vgacentrifuge/pcb/centrifuge_combined/centrifuge.kicad_sch

## KiCad design centrifuge_combined/centrifuge.kicad_sch (2022-10-28)

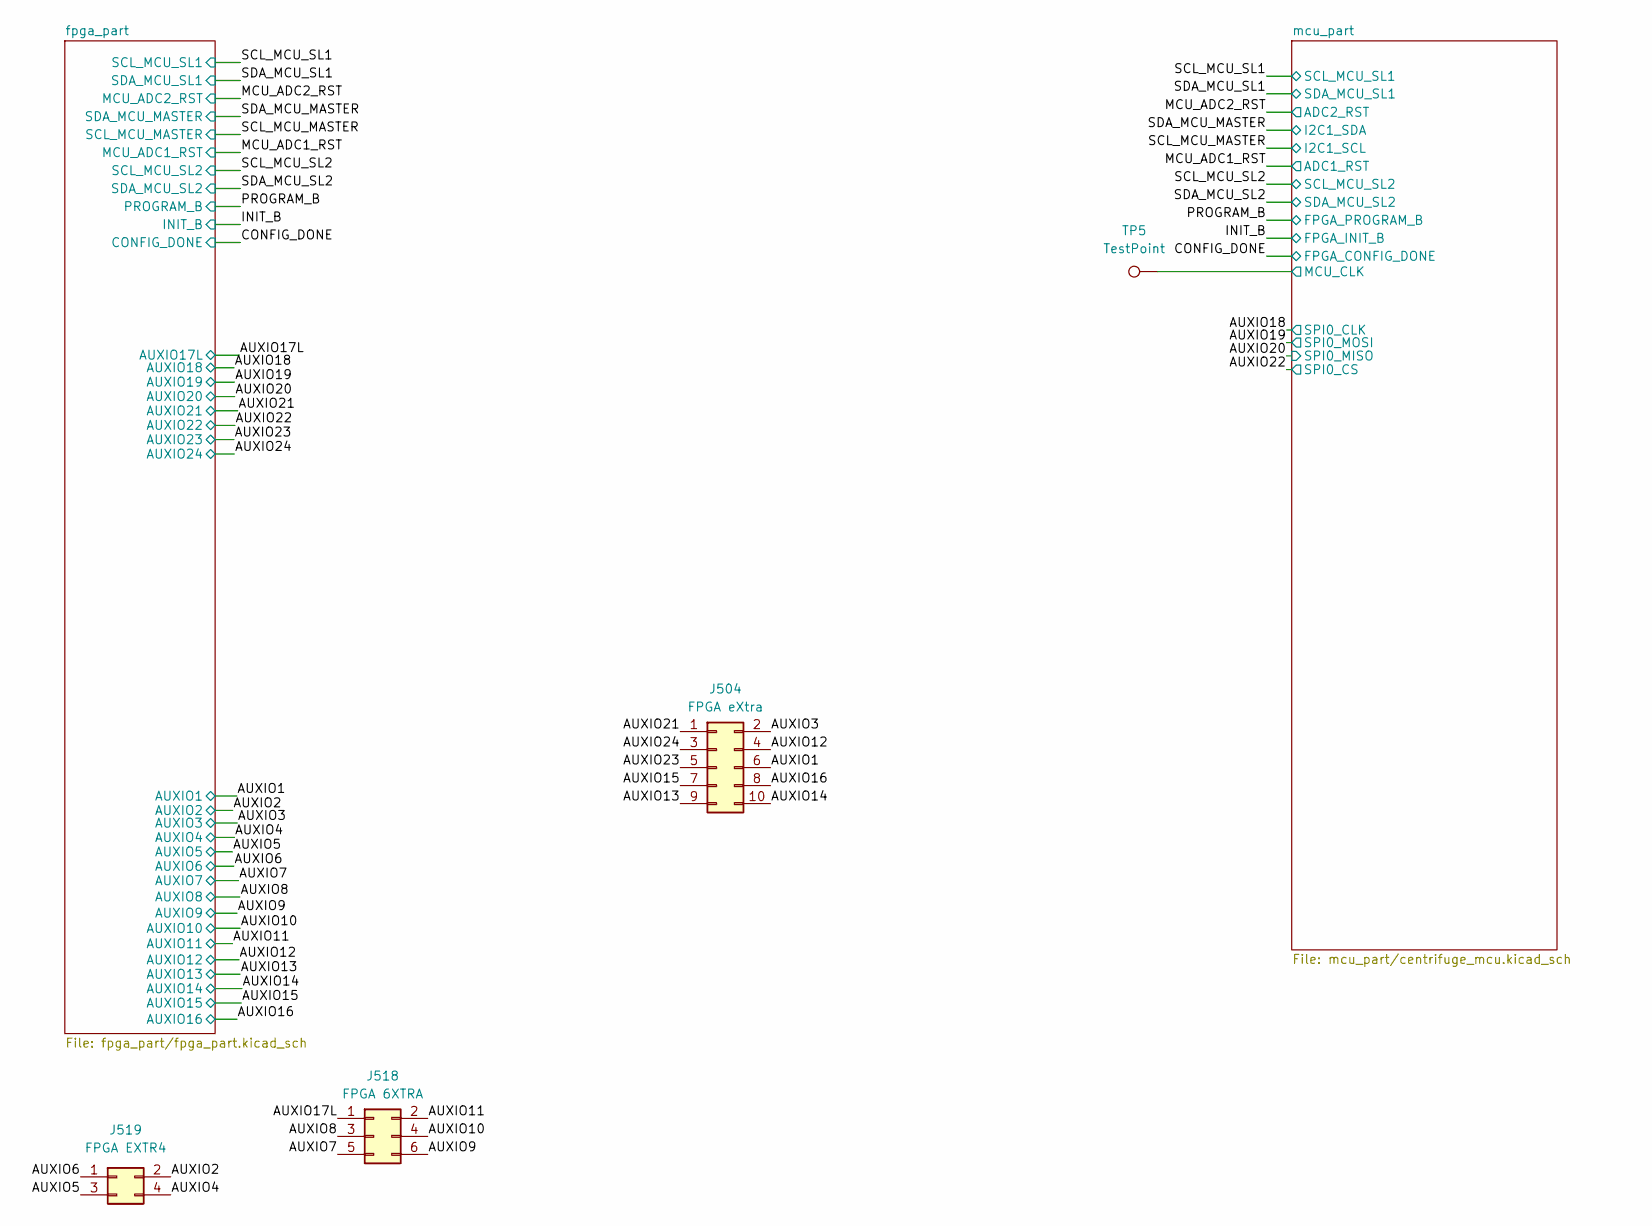
[picture p18: schematic centrifuge.kicad_sch]

Parts:
J504: FPGA eXtra; PinHeader_2x05_P2.54mm_Vertical
J518: FPGA 6XTRA; PinHeader_2x03_P2.54mm_Vertical
J519: FPGA EXTR4; PinHeader_2x02_P2.54mm_Vertical
TP5: TestPoint; TestPoint_Keystone_5015_Micro-Minature

Connections:
AUXIO1: J504.6
AUXIO2: J519.2
AUXIO3: J504.2
AUXIO4: J519.4
AUXIO5: J519.3
AUXIO6: J519.1
AUXIO7: J518.5
AUXIO8: J518.3
AUXIO9: J518.6
AUXIO10: J518.4
AUXIO11: J518.2
AUXIO12: J504.4
AUXIO13: J504.9
AUXIO14: J504.10
AUXIO15: J504.7
AUXIO16: J504.8
AUXIO17L: J518.1
AUXIO21: J504.1
AUXIO23: J504.5
AUXIO24: J504.3
MCU_CLK: TP5.1
