vgacentrifuge/pcb/centrifuge_combined/fpga_part/config_sram.kicad_sch

## KiCad design centrifuge_combined/fpga_part/config_sram.kicad_sch (2022-10-22)

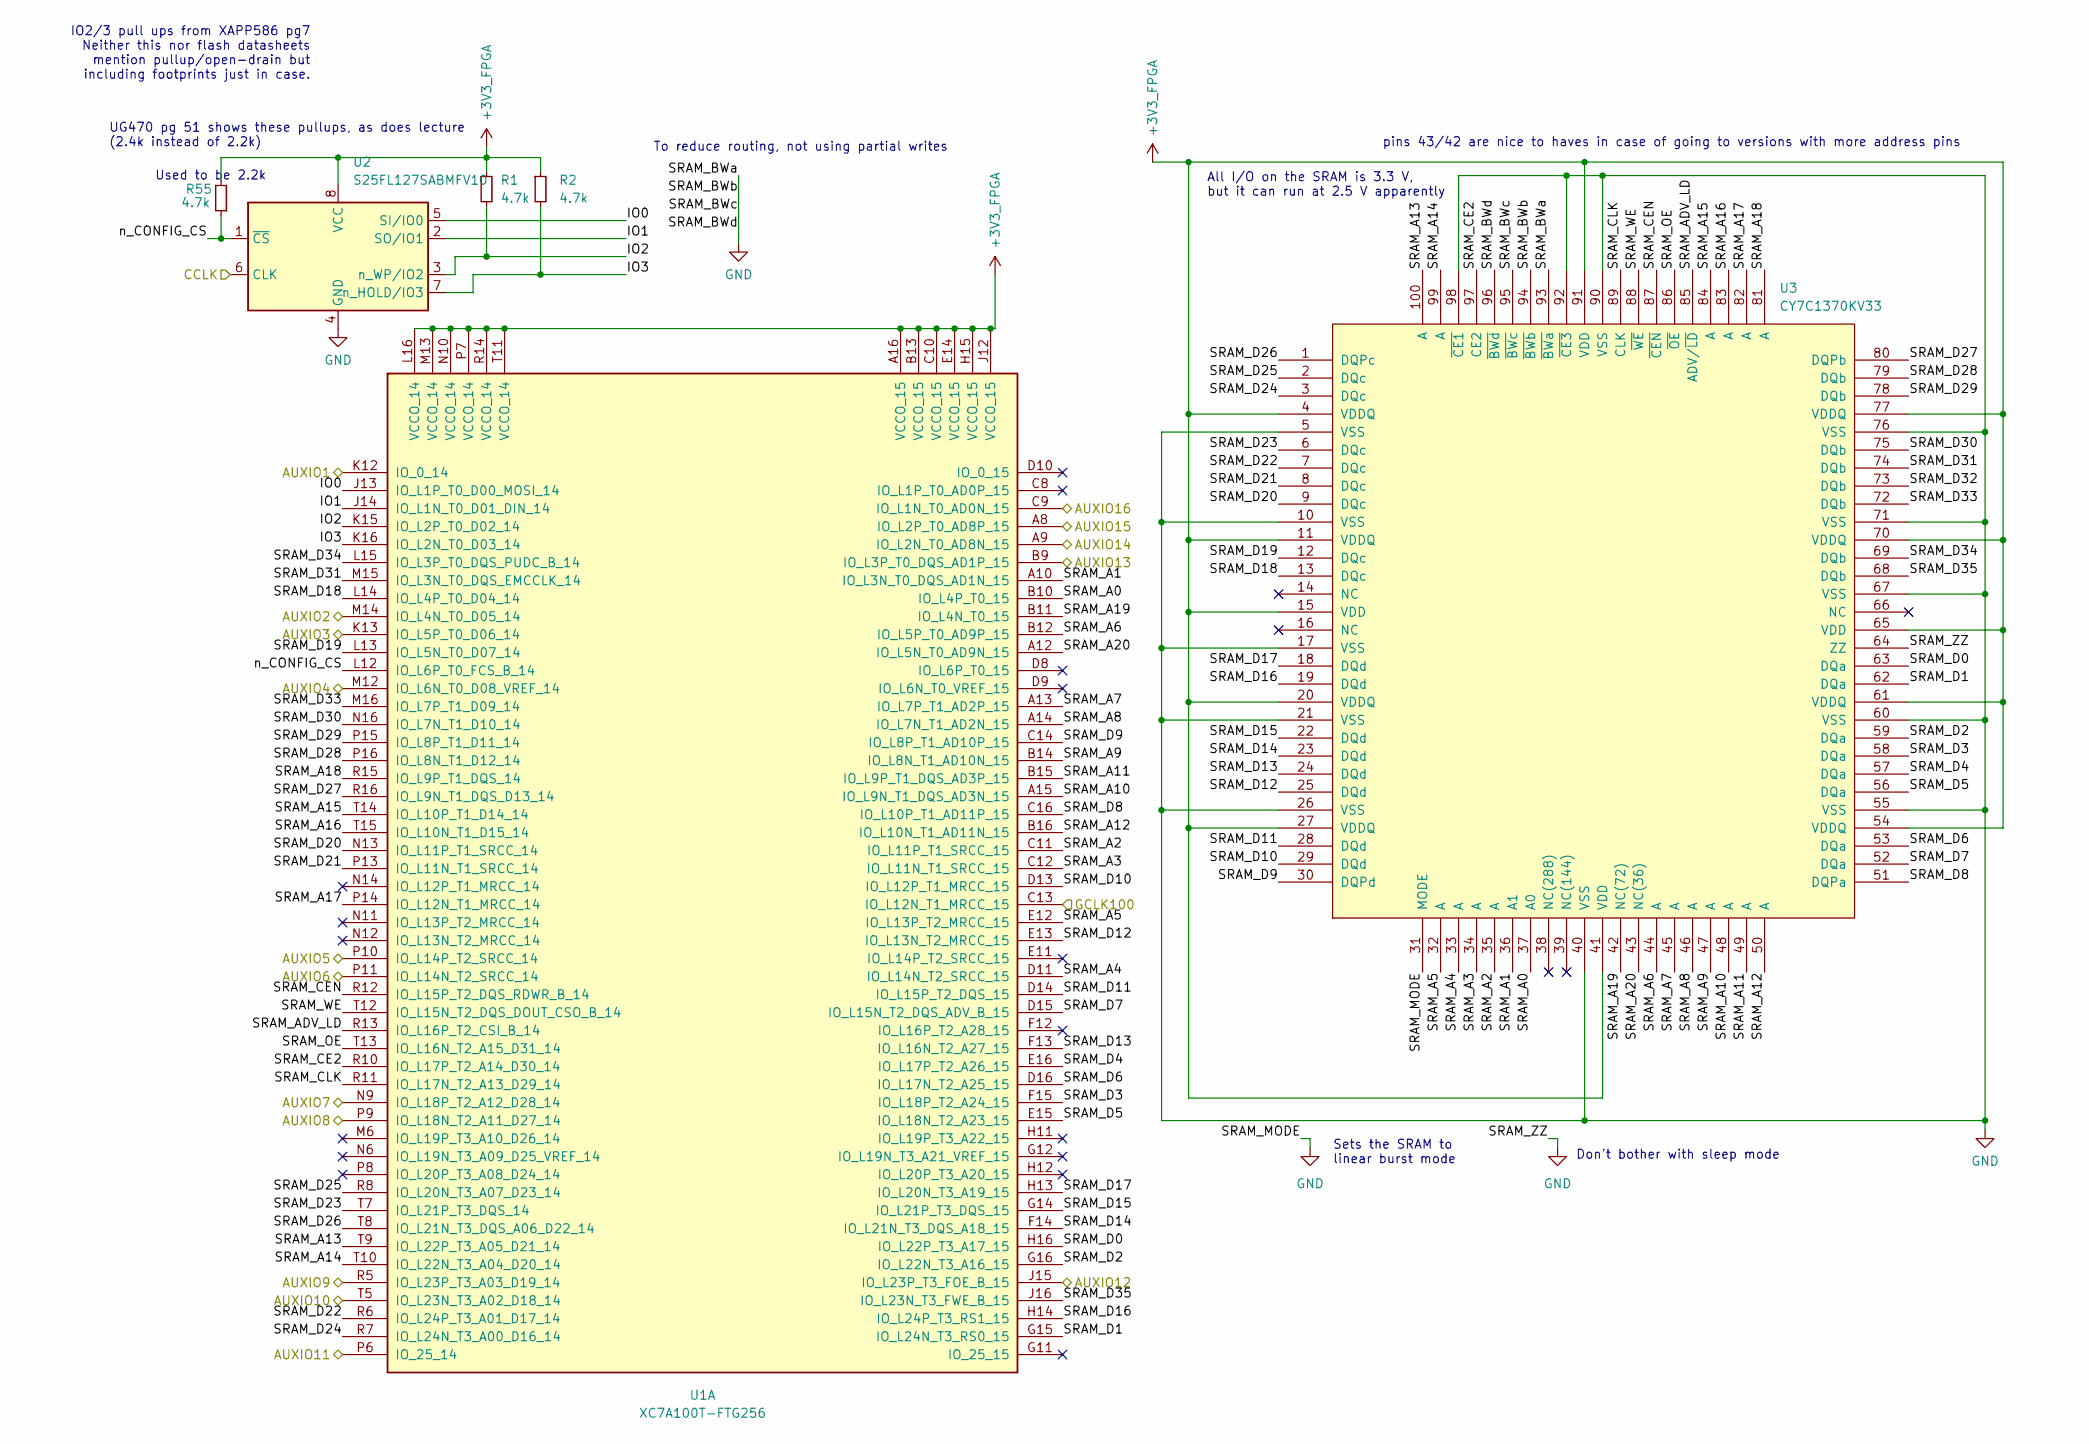
[picture p19: schematic config_sram.kicad_sch]

Parts:
R1, R2, R55: 4.7k; R_0805_2012Metric_Pad1.20x1.40mm_HandSolder
U1: XC7A100T-FTG256; Xilinx_FTG256
U2: S25FL127SABMFV10; SOIC-8_5.23x5.23mm_P1.27mm
U3: CY7C1370KV33; PQFP-100_14x20mm_P0.65mm

Connections:
+3V3_FPGA: R1.1, R2.1, R55.2, U1.A16 (VCCO_15), U1.B13 (VCCO_15), U1.C10 (VCCO_15), U1.E14 (VCCO_15), U1.H15 (VCCO_15), U1.J12 (VCCO_15), U1.L16 (VCCO_14), U1.M13 (VCCO_14), U1.N10 (VCCO_14), U1.P7 (VCCO_14), U1.R14 (VCCO_14), U1.T11 (VCCO_14), U2.8 (VCC), U3.4 (VDDQ), U3.11 (VDDQ), U3.15 (VDD), U3.20 (VDDQ), U3.27 (VDDQ), U3.41 (VDD), U3.54 (VDDQ), U3.61 (VDDQ), U3.65 (VDD), U3.70 (VDDQ), U3.77 (VDDQ), U3.91 (VDD)
AUXIO1: U1.K12 (IO_0_14)
AUXIO2: U1.M14 (IO_L4N_T0_D05_14)
AUXIO3: U1.K13 (IO_L5P_T0_D06_14)
AUXIO4: U1.M12 (IO_L6N_T0_D08_VREF_14)
AUXIO5: U1.P10 (IO_L14P_T2_SRCC_14)
AUXIO6: U1.P11 (IO_L14N_T2_SRCC_14)
AUXIO7: U1.N9 (IO_L18P_T2_A12_D28_14)
AUXIO8: U1.P9 (IO_L18N_T2_A11_D27_14)
AUXIO9: U1.R5 (IO_L23P_T3_A03_D19_14)
AUXIO10: U1.T5 (IO_L23N_T3_A02_D18_14)
AUXIO11: U1.P6 (IO_25_14)
AUXIO12: U1.J15 (IO_L23P_T3_FOE_B_15)
AUXIO13: U1.B9 (IO_L3P_T0_DQS_AD1P_15)
AUXIO14: U1.A9 (IO_L2N_T0_AD8N_15)
AUXIO15: U1.A8 (IO_L2P_T0_AD8P_15)
AUXIO16: U1.C9 (IO_L1N_T0_AD0N_15)
CCLK: U2.6 (CLK)
GCLK100: U1.C13 (IO_L12N_T1_MRCC_15)
GND: U2.4 (GND), U3.5 (VSS), U3.10 (VSS), U3.17 (VSS), U3.21 (VSS), U3.26 (VSS), U3.31 (MODE), U3.40 (VSS), U3.55 (VSS), U3.60 (VSS), U3.64 (ZZ), U3.67 (VSS), U3.71 (VSS), U3.76 (VSS), U3.90 (VSS), U3.92 (~CE3), U3.93 (~BWa), U3.94 (~BWb), U3.95 (~BWc), U3.96 (~BWd), U3.98 (~CE1)
IO0: U1.J13 (IO_L1P_T0_D00_MOSI_14), U2.5 (SI/IO0)
IO1: U1.J14 (IO_L1N_T0_D01_DIN_14), U2.2 (SO/IO1)
IO2: R1.2, U1.K15 (IO_L2P_T0_D02_14), U2.3 (n_WP/IO2)
IO3: R2.2, U1.K16 (IO_L2N_T0_D03_14), U2.7 (n_HOLD/IO3)
SRAM_A0: U1.B10 (IO_L4P_T0_15), U3.37 (A0)
SRAM_A1: U1.A10 (IO_L3N_T0_DQS_AD1N_15), U3.36 (A1)
SRAM_A2: U1.C11 (IO_L11P_T1_SRCC_15), U3.35 (A)
SRAM_A3: U1.C12 (IO_L11N_T1_SRCC_15), U3.34 (A)
SRAM_A4: U1.D11 (IO_L14N_T2_SRCC_15), U3.33 (A)
SRAM_A5: U1.E12 (IO_L13P_T2_MRCC_15), U3.32 (A)
SRAM_A6: U1.B12 (IO_L5P_T0_AD9P_15), U3.44 (A)
SRAM_A7: U1.A13 (IO_L7P_T1_AD2P_15), U3.45 (A)
SRAM_A8: U1.A14 (IO_L7N_T1_AD2N_15), U3.46 (A)
SRAM_A9: U1.B14 (IO_L8N_T1_AD10N_15), U3.47 (A)
SRAM_A10: U1.A15 (IO_L9N_T1_DQS_AD3N_15), U3.48 (A)
SRAM_A11: U1.B15 (IO_L9P_T1_DQS_AD3P_15), U3.49 (A)
SRAM_A12: U1.B16 (IO_L10N_T1_AD11N_15), U3.50 (A)
SRAM_A13: U1.T9 (IO_L22P_T3_A05_D21_14), U3.100 (A)
SRAM_A14: U1.T10 (IO_L22N_T3_A04_D20_14), U3.99 (A)
SRAM_A15: U1.T14 (IO_L10P_T1_D14_14), U3.84 (A)
SRAM_A16: U1.T15 (IO_L10N_T1_D15_14), U3.83 (A)
SRAM_A17: U1.P14 (IO_L12N_T1_MRCC_14), U3.82 (A)
SRAM_A18: U1.R15 (IO_L9P_T1_DQS_14), U3.81 (A)
SRAM_A19: U1.B11 (IO_L4N_T0_15), U3.42 (NC(72))
SRAM_A20: U1.A12 (IO_L5N_T0_AD9N_15), U3.43 (NC(36))
SRAM_ADV_LD: U1.R13 (IO_L16P_T2_CSI_B_14), U3.85 (ADV/~LD)
SRAM_CE2: U1.R10 (IO_L17P_T2_A14_D30_14), U3.97 (CE2)
SRAM_CEN: U1.R12 (IO_L15P_T2_DQS_RDWR_B_14), U3.87 (~CEN)
SRAM_CLK: U1.R11 (IO_L17N_T2_A13_D29_14), U3.89 (CLK)
SRAM_D0: U1.H16 (IO_L22P_T3_A17_15), U3.63 (DQa)
SRAM_D1: U1.G15 (IO_L24N_T3_RS0_15), U3.62 (DQa)
SRAM_D2: U1.G16 (IO_L22N_T3_A16_15), U3.59 (DQa)
SRAM_D3: U1.F15 (IO_L18P_T2_A24_15), U3.58 (DQa)
SRAM_D4: U1.E16 (IO_L17P_T2_A26_15), U3.57 (DQa)
SRAM_D5: U1.E15 (IO_L18N_T2_A23_15), U3.56 (DQa)
SRAM_D6: U1.D16 (IO_L17N_T2_A25_15), U3.53 (DQa)
SRAM_D7: U1.D15 (IO_L15N_T2_DQS_ADV_B_15), U3.52 (DQa)
SRAM_D8: U1.C16 (IO_L10P_T1_AD11P_15), U3.51 (DQPa)
SRAM_D9: U1.C14 (IO_L8P_T1_AD10P_15), U3.30 (DQPd)
SRAM_D10: U1.D13 (IO_L12P_T1_MRCC_15), U3.29 (DQd)
SRAM_D11: U1.D14 (IO_L15P_T2_DQS_15), U3.28 (DQd)
SRAM_D12: U1.E13 (IO_L13N_T2_MRCC_15), U3.25 (DQd)
SRAM_D13: U1.F13 (IO_L16N_T2_A27_15), U3.24 (DQd)
SRAM_D14: U1.F14 (IO_L21N_T3_DQS_A18_15), U3.23 (DQd)
SRAM_D15: U1.G14 (IO_L21P_T3_DQS_15), U3.22 (DQd)
SRAM_D16: U1.H14 (IO_L24P_T3_RS1_15), U3.19 (DQd)
SRAM_D17: U1.H13 (IO_L20N_T3_A19_15), U3.18 (DQd)
SRAM_D18: U1.L14 (IO_L4P_T0_D04_14), U3.13 (DQc)
SRAM_D19: U1.L13 (IO_L5N_T0_D07_14), U3.12 (DQc)
SRAM_D20: U1.N13 (IO_L11P_T1_SRCC_14), U3.9 (DQc)
SRAM_D21: U1.P13 (IO_L11N_T1_SRCC_14), U3.8 (DQc)
SRAM_D22: U1.R6 (IO_L24P_T3_A01_D17_14), U3.7 (DQc)
SRAM_D23: U1.T7 (IO_L21P_T3_DQS_14), U3.6 (DQc)
SRAM_D24: U1.R7 (IO_L24N_T3_A00_D16_14), U3.3 (DQc)
SRAM_D25: U1.R8 (IO_L20N_T3_A07_D23_14), U3.2 (DQc)
SRAM_D26: U1.T8 (IO_L21N_T3_DQS_A06_D22_14), U3.1 (DQPc)
SRAM_D27: U1.R16 (IO_L9N_T1_DQS_D13_14), U3.80 (DQPb)
SRAM_D28: U1.P16 (IO_L8N_T1_D12_14), U3.79 (DQb)
SRAM_D29: U1.P15 (IO_L8P_T1_D11_14), U3.78 (DQb)
SRAM_D30: U1.N16 (IO_L7N_T1_D10_14), U3.75 (DQb)
SRAM_D31: U1.M15 (IO_L3N_T0_DQS_EMCCLK_14), U3.74 (DQb)
SRAM_D32: U3.73 (DQb)
SRAM_D33: U1.M16 (IO_L7P_T1_D09_14), U3.72 (DQb)
SRAM_D34: U1.L15 (IO_L3P_T0_DQS_PUDC_B_14), U3.69 (DQb)
SRAM_D35: U1.J16 (IO_L23N_T3_FWE_B_15), U3.68 (DQb)
SRAM_OE: U1.T13 (IO_L16N_T2_A15_D31_14), U3.86 (~OE)
SRAM_WE: U1.T12 (IO_L15N_T2_DQS_DOUT_CSO_B_14), U3.88 (~WE)
n_CONFIG_CS: R55.1, U1.L12 (IO_L6P_T0_FCS_B_14), U2.1 (~CS)

Notes on the sheet:
Don't bother with sleep mode
Sets the SRAM to linear burst mode
Used to be 2.2k
IO2/3 pull ups from XAPP586 pg7 Neither this nor flash datasheets mention pullup/open-drain but including footprints just in case.
UG470 pg 51 shows these pullups, as does lecture (2.4k instead of 2.2k)
All I/O on the SRAM is 3.3 V, but it can run at 2.5 V apparently
To reduce routing, not using partial writes
pins 43/42 are nice to haves in case of going to versions with more address pins
