vgacentrifuge/pcb/centrifuge_combined/fpga_part/ddc_eeprom.kicad_sch

## KiCad design centrifuge_combined/fpga_part/ddc_eeprom.kicad_sch (2022-11-09)

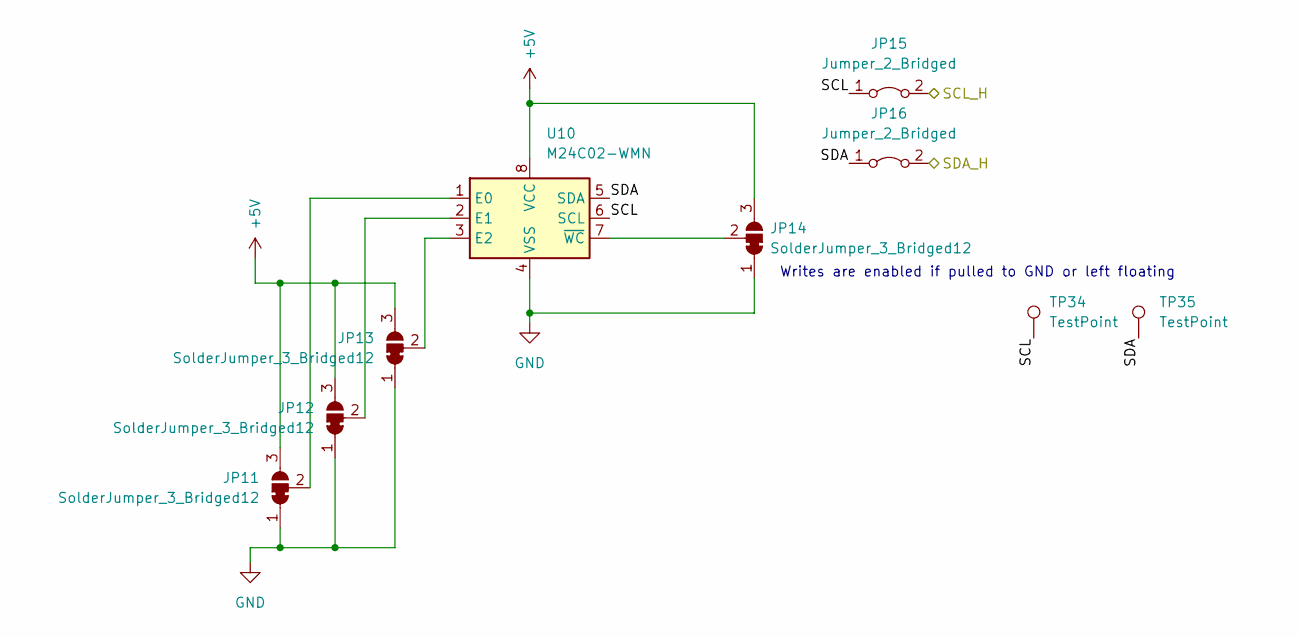
[picture p20: schematic ddc_eeprom.kicad_sch]

Parts:
JP11, JP12, JP13, JP14: SolderJumper_3_Bridged12; SolderJumper-3_P1.3mm_Open_Pad1.0x1.5mm_NumberLabels
JP15, JP16: Jumper_2_Bridged; SolderJumper-2_P1.3mm_Bridged_Pad1.0x1.5mm
TP34, TP35: TestPoint; TestPoint_Keystone_5015_Micro-Minature
U10: M24C02-WMN; SOIC-8_3.9x4.9mm_P1.27mm

Connections:
+5V: JP11.3 (B), JP12.3 (B), JP13.3 (B), JP14.3 (B), U10.8 (VCC)
GND: JP11.1 (A), JP12.1 (A), JP13.1 (A), JP14.1 (A), U10.4 (VSS)
unnamed: JP11.2 (C), U10.1 (E0)
unnamed: JP12.2 (C), U10.2 (E1)
unnamed: JP13.2 (C), U10.3 (E2)
unnamed: JP14.2 (C), U10.7 (~WC)
SCL: JP15.1 (A), TP34.1, U10.6 (SCL)
SCL_H: JP15.2 (B)
SDA: JP16.1 (A), TP35.1, U10.5 (SDA)
SDA_H: JP16.2 (B)

Notes on the sheet:
Writes are enabled if pulled to GND or left floating
