vgacentrifuge/pcb/centrifuge_combined/fpga_part/fpga_core.kicad_sch

## KiCad design centrifuge_combined/fpga_part/fpga_core.kicad_sch (2022-11-09)

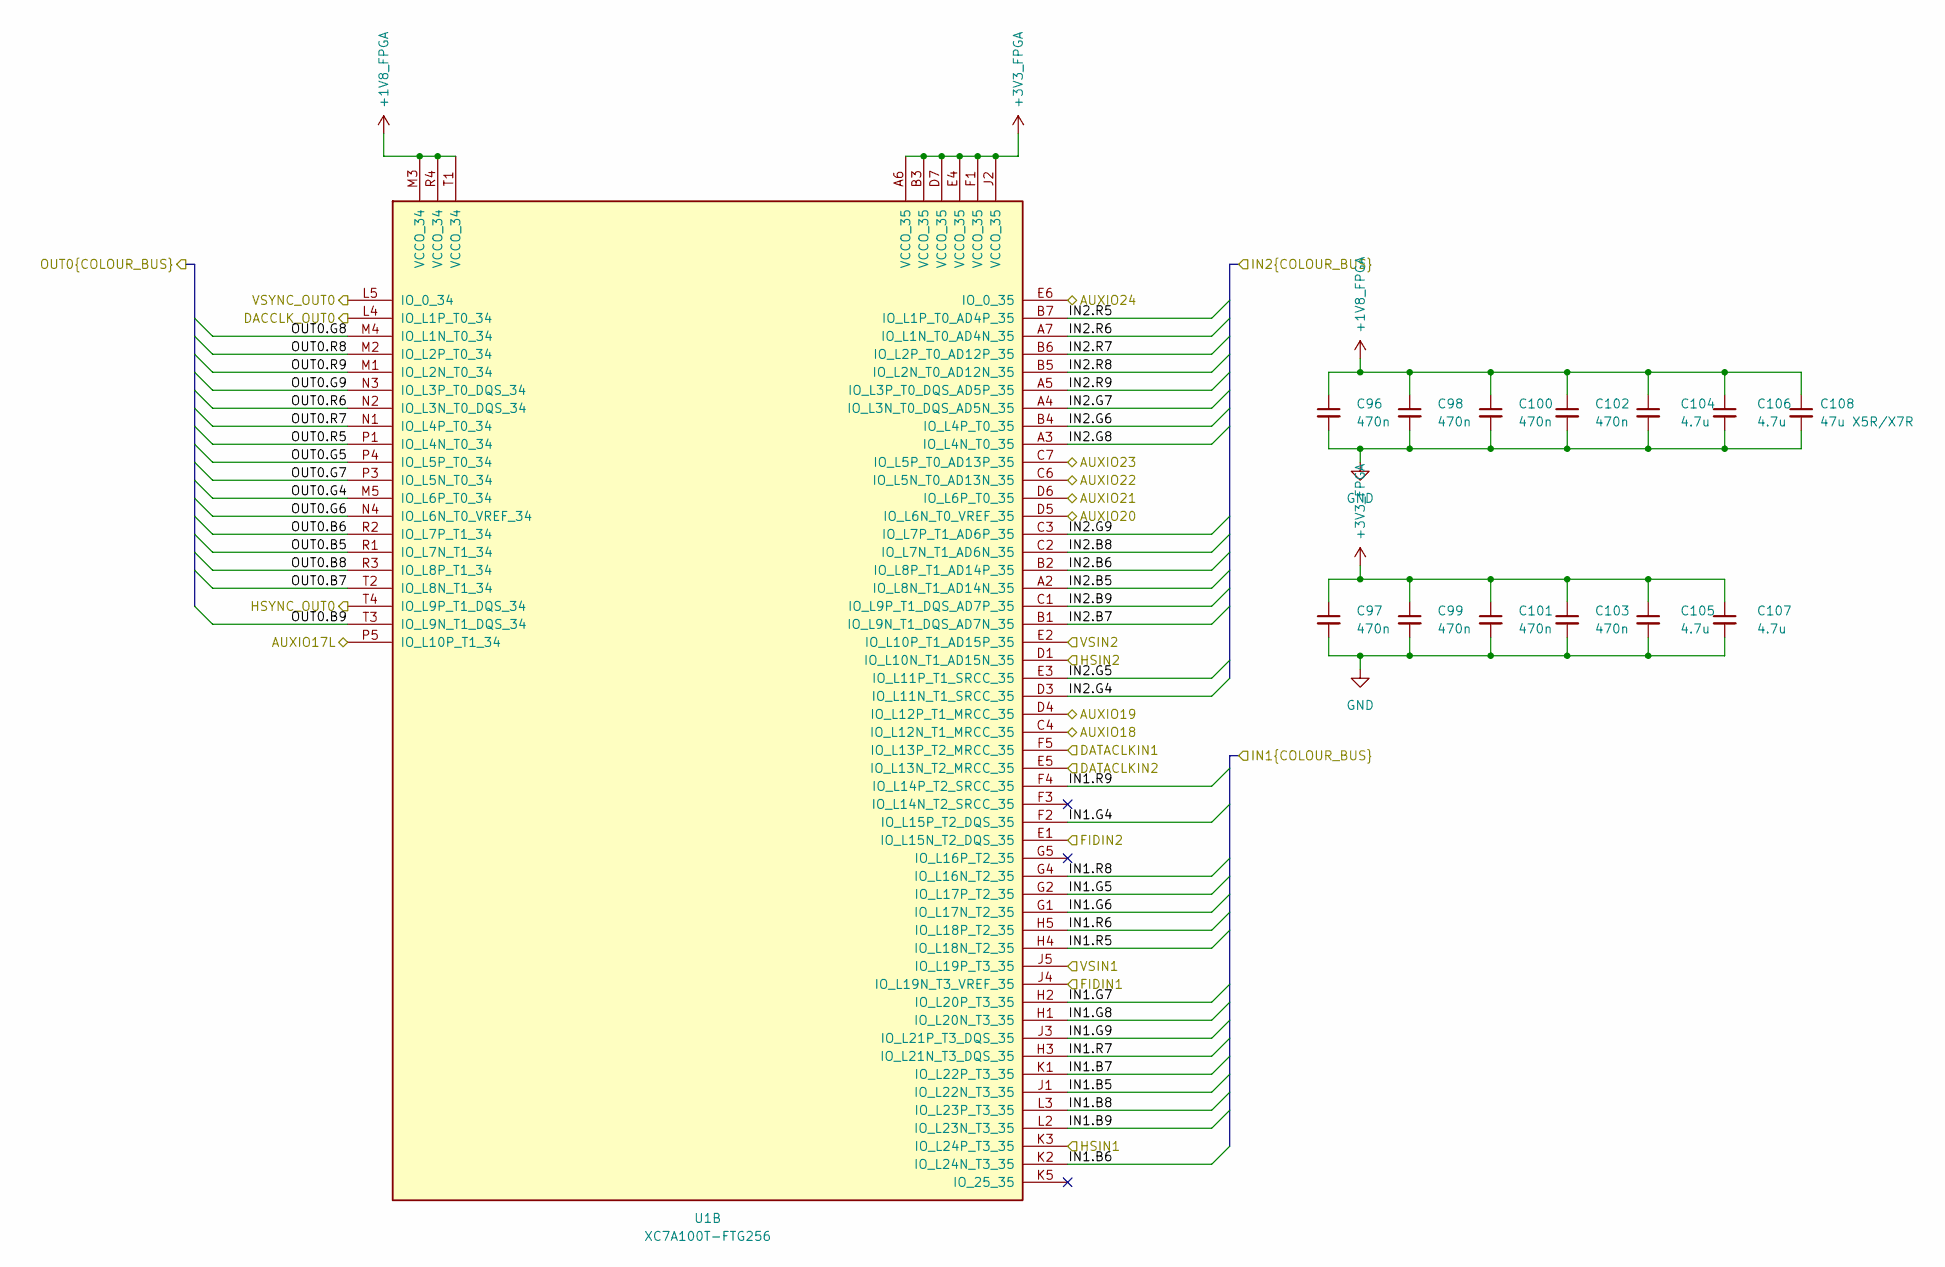
[picture p21: schematic fpga_core.kicad_sch]

Parts:
C96, C97, C98, C99, C100, C101, C102, C103: 470n; C_0603_1608Metric_Pad1.08x0.95mm_HandSolder
C104, C105, C106, C107: 4.7u; C_0805_2012Metric_Pad1.18x1.45mm_HandSolder
C108: 47u X5R/X7R; C_1210_3225Metric_Pad1.33x2.70mm_HandSolder
U1: XC7A100T-FTG256; Xilinx_FTG256

Connections:
+1V8_FPGA: C96.1, C98.1, C100.1, C102.1, C104.1, C106.1, C108.1, U1.M3 (VCCO_34), U1.R4 (VCCO_34), U1.T1 (VCCO_34)
+3V3_FPGA: C97.1, C99.1, C101.1, C103.1, C105.1, C107.1, U1.A6 (VCCO_35), U1.B3 (VCCO_35), U1.D7 (VCCO_35), U1.E4 (VCCO_35), U1.F1 (VCCO_35), U1.J2 (VCCO_35)
AUXIO17L: U1.P5 (IO_L10P_T1_34)
AUXIO18: U1.C4 (IO_L12N_T1_MRCC_35)
AUXIO19: U1.D4 (IO_L12P_T1_MRCC_35)
AUXIO20: U1.D5 (IO_L6N_T0_VREF_35)
AUXIO21: U1.D6 (IO_L6P_T0_35)
AUXIO22: U1.C6 (IO_L5N_T0_AD13N_35)
AUXIO23: U1.C7 (IO_L5P_T0_AD13P_35)
AUXIO24: U1.E6 (IO_0_35)
DACCLK_OUT0: U1.L4 (IO_L1P_T0_34)
DATACLKIN1: U1.F5 (IO_L13P_T2_MRCC_35)
DATACLKIN2: U1.E5 (IO_L13N_T2_MRCC_35)
FIDIN1: U1.J4 (IO_L19N_T3_VREF_35)
FIDIN2: U1.E1 (IO_L15N_T2_DQS_35)
GND: C96.2, C97.2, C98.2, C99.2, C100.2, C101.2, C102.2, C103.2, C104.2, C105.2, C106.2, C107.2, C108.2
HSIN1: U1.K3 (IO_L24P_T3_35)
HSIN2: U1.D1 (IO_L10N_T1_AD15N_35)
HSYNC_OUT0: U1.T4 (IO_L9P_T1_DQS_34)
IN1.B5: U1.J1 (IO_L22N_T3_35)
IN1.B6: U1.K2 (IO_L24N_T3_35)
IN1.B7: U1.K1 (IO_L22P_T3_35)
IN1.B8: U1.L3 (IO_L23P_T3_35)
IN1.B9: U1.L2 (IO_L23N_T3_35)
IN1.G4: U1.F2 (IO_L15P_T2_DQS_35)
IN1.G5: U1.G2 (IO_L17P_T2_35)
IN1.G6: U1.G1 (IO_L17N_T2_35)
IN1.G7: U1.H2 (IO_L20P_T3_35)
IN1.G8: U1.H1 (IO_L20N_T3_35)
IN1.G9: U1.J3 (IO_L21P_T3_DQS_35)
IN1.R5: U1.H4 (IO_L18N_T2_35)
IN1.R6: U1.H5 (IO_L18P_T2_35)
IN1.R7: U1.H3 (IO_L21N_T3_DQS_35)
IN1.R8: U1.G4 (IO_L16N_T2_35)
IN1.R9: U1.F4 (IO_L14P_T2_SRCC_35)
IN2.B5: U1.A2 (IO_L8N_T1_AD14N_35)
IN2.B6: U1.B2 (IO_L8P_T1_AD14P_35)
IN2.B7: U1.B1 (IO_L9N_T1_DQS_AD7N_35)
IN2.B8: U1.C2 (IO_L7N_T1_AD6N_35)
IN2.B9: U1.C1 (IO_L9P_T1_DQS_AD7P_35)
IN2.G4: U1.D3 (IO_L11N_T1_SRCC_35)
IN2.G5: U1.E3 (IO_L11P_T1_SRCC_35)
IN2.G6: U1.B4 (IO_L4P_T0_35)
IN2.G7: U1.A4 (IO_L3N_T0_DQS_AD5N_35)
IN2.G8: U1.A3 (IO_L4N_T0_35)
IN2.G9: U1.C3 (IO_L7P_T1_AD6P_35)
IN2.R5: U1.B7 (IO_L1P_T0_AD4P_35)
IN2.R6: U1.A7 (IO_L1N_T0_AD4N_35)
IN2.R7: U1.B6 (IO_L2P_T0_AD12P_35)
IN2.R8: U1.B5 (IO_L2N_T0_AD12N_35)
IN2.R9: U1.A5 (IO_L3P_T0_DQS_AD5P_35)
OUT0.B5: U1.R1 (IO_L7N_T1_34)
OUT0.B6: U1.R2 (IO_L7P_T1_34)
OUT0.B7: U1.T2 (IO_L8N_T1_34)
OUT0.B8: U1.R3 (IO_L8P_T1_34)
OUT0.B9: U1.T3 (IO_L9N_T1_DQS_34)
OUT0.G4: U1.M5 (IO_L6P_T0_34)
OUT0.G5: U1.P4 (IO_L5P_T0_34)
OUT0.G6: U1.N4 (IO_L6N_T0_VREF_34)
OUT0.G7: U1.P3 (IO_L5N_T0_34)
OUT0.G8: U1.M4 (IO_L1N_T0_34)
OUT0.G9: U1.N3 (IO_L3P_T0_DQS_34)
OUT0.R5: U1.P1 (IO_L4N_T0_34)
OUT0.R6: U1.N2 (IO_L3N_T0_DQS_34)
OUT0.R7: U1.N1 (IO_L4P_T0_34)
OUT0.R8: U1.M2 (IO_L2P_T0_34)
OUT0.R9: U1.M1 (IO_L2N_T0_34)
VSIN1: U1.J5 (IO_L19P_T3_35)
VSIN2: U1.E2 (IO_L10P_T1_AD15P_35)
VSYNC_OUT0: U1.L5 (IO_0_34)
