vgacentrifuge/pcb/centrifuge_combined/fpga_part/fpga_part.kicad_sch

## KiCad design centrifuge_combined/fpga_part/fpga_part.kicad_sch (2022-11-09)

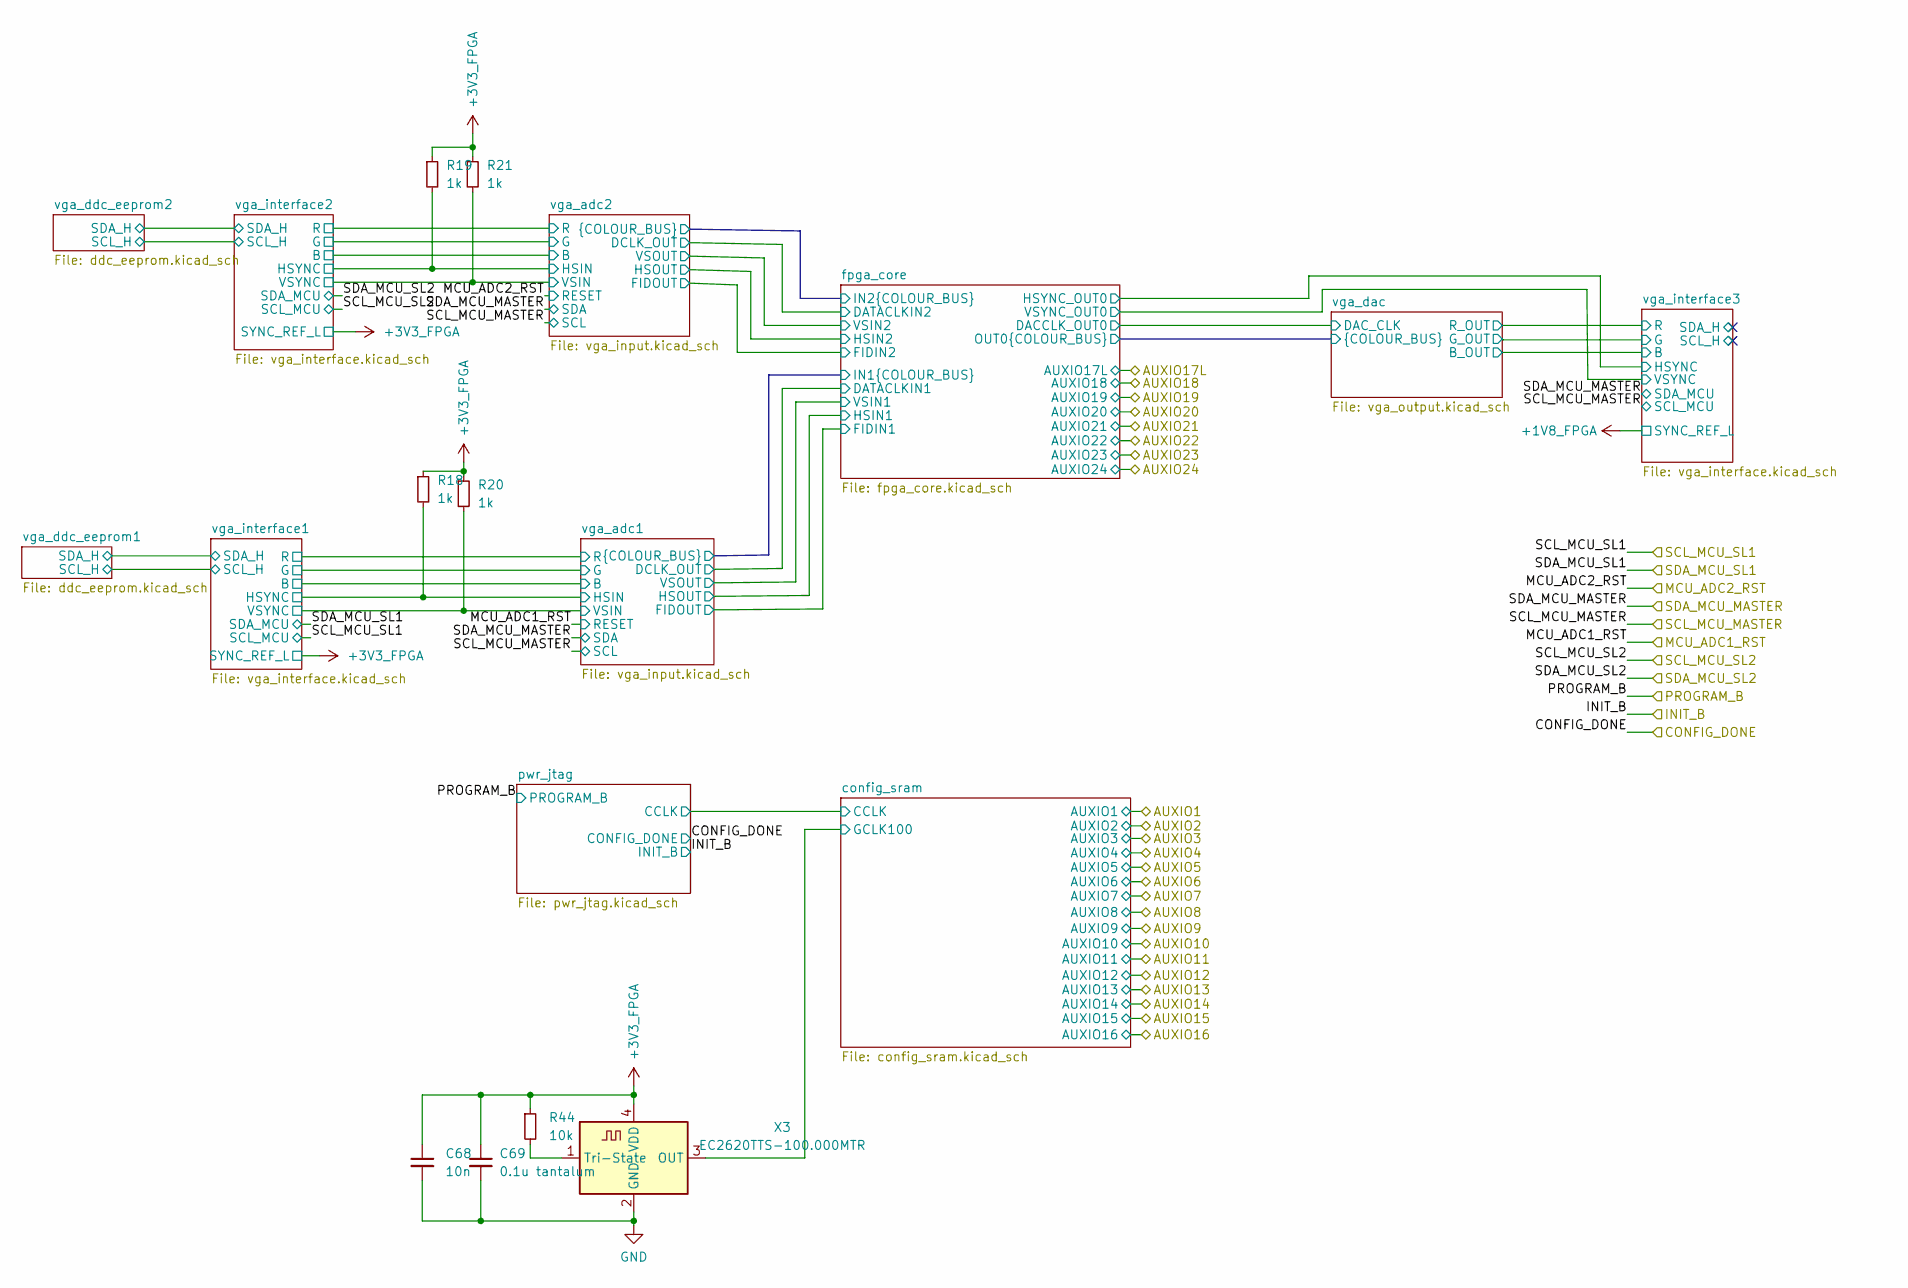
[picture p22: schematic fpga_part.kicad_sch]

Parts:
C68: 10n; C_0805_2012Metric_Pad1.18x1.45mm_HandSolder
C69: 0.1u tantalum; C_0805_2012Metric_Pad1.18x1.45mm_HandSolder
R18, R19, R20, R21: 1k; R_0805_2012Metric_Pad1.20x1.40mm_HandSolder
R44: 10k; R_0805_2012Metric_Pad1.20x1.40mm_HandSolder
X3: EC2620TTS-100.000MTR; Oscillator_SMD_EuroQuartz_XO91-4Pin_7.0x5.0mm_HandSoldering

Connections:
+3V3_FPGA: C68.1, C69.1, R18.1, R19.1, R20.1, R21.1, R44.1, X3.4 (VDD)
GCLK100: X3.3 (OUT)
GND: C68.2, C69.2, X3.2 (GND)
HSYNC: R18.2, R19.2
unnamed: R44.2, X3.1 (Tri-State)
VSYNC: R20.2, R21.2
