vgacentrifuge/pcb/centrifuge_combined/fpga_part/pwr_jtag.kicad_sch

## KiCad design centrifuge_combined/fpga_part/pwr_jtag.kicad_sch (2022-10-13)

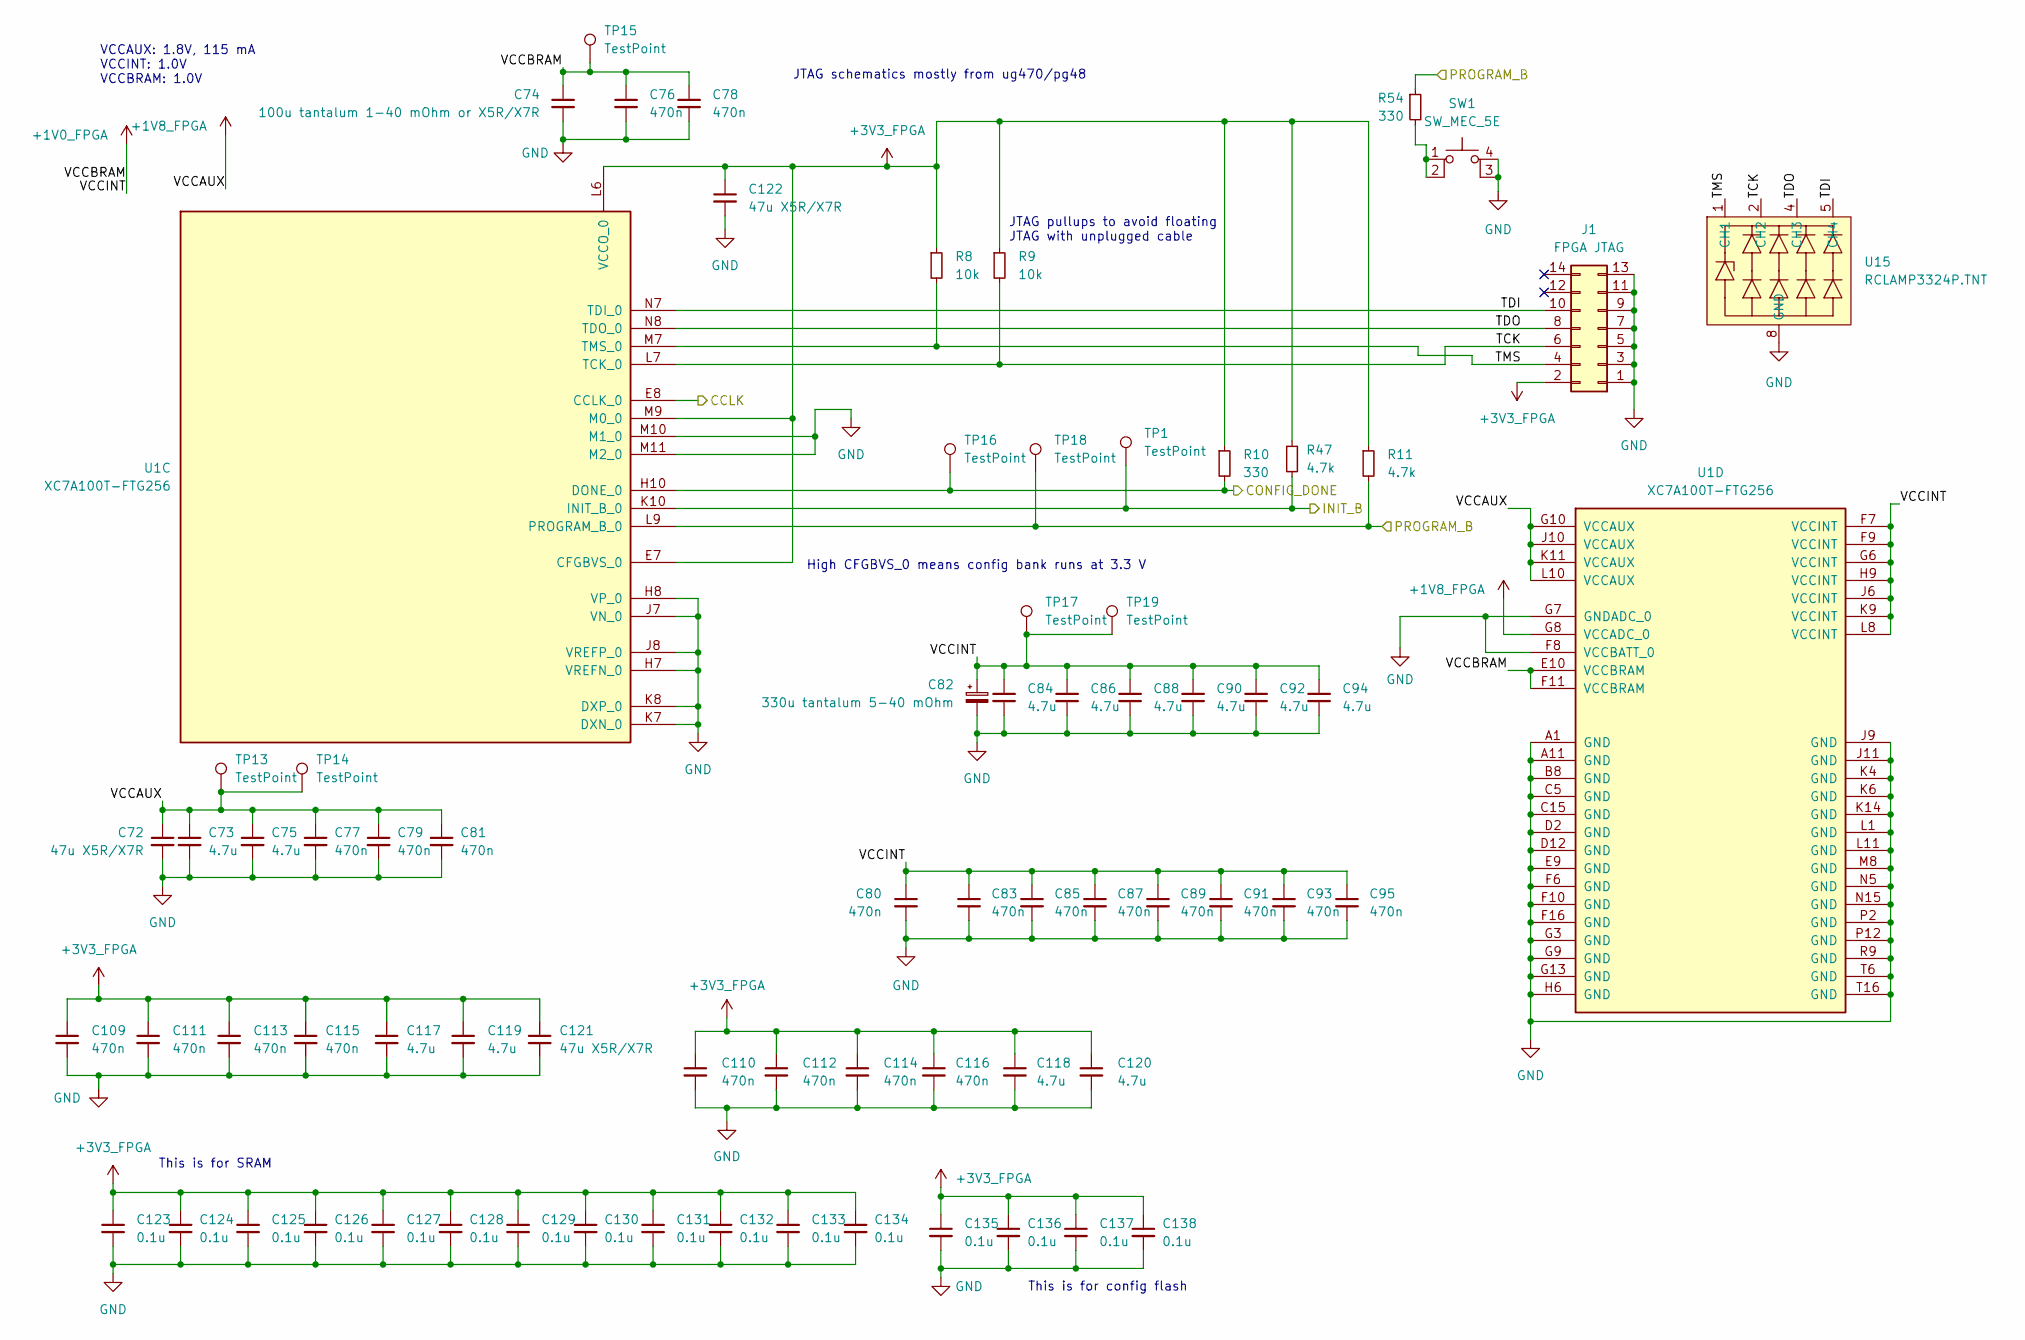
[picture p23: schematic pwr_jtag.kicad_sch]

Parts:
C72, C121, C122: 47u X5R/X7R; C_1210_3225Metric_Pad1.33x2.70mm_HandSolder
C73, C75, C84, C86, C88, C90, C92, C94, C117, C118, C119, C120: 4.7u; C_0805_2012Metric_Pad1.18x1.45mm_HandSolder
C74: 100u tantalum 1-40 mOhm or X5R/X7R; C_1210_3225Metric_Pad1.33x2.70mm_HandSolder
C76, C77, C78, C79, C80, C81, C83, C85, C87, C89, C91, C93, C95, C109, C110, C111, C112, C113, C114, C115, C116: 470n; C_0603_1608Metric_Pad1.08x0.95mm_HandSolder
C82: 330u tantalum 5-40 mOhm; CP_EIA-7343-31_Kemet-D_Pad2.25x2.55mm_HandSolder
C123, C124, C125, C126, C127, C128, C129, C130, C131, C132, C133, C134, C135, C136, C137, C138: 0.1u; C_0805_2012Metric_Pad1.18x1.45mm_HandSolder
J1: FPGA JTAG; 878311411
R8, R9: 10k; R_0805_2012Metric_Pad1.20x1.40mm_HandSolder
R10, R54: 330; R_0805_2012Metric_Pad1.20x1.40mm_HandSolder
R11, R47: 4.7k; R_0805_2012Metric_Pad1.20x1.40mm_HandSolder
SW1: SW_MEC_5E; SW_Push_1P1T_NO_6x6mm_H9.5mm_modified
TP1, TP13, TP14, TP15, TP16, TP17, TP18, TP19: TestPoint; TestPoint_Keystone_5015_Micro-Minature
U1: XC7A100T-FTG256; Xilinx_FTG256
U15: RCLAMP3324P.TNT; Diodes_UDFN-10_1.0x2.5mm_P0.5mm

Connections:
+1V0_FPGA: C74.1, C76.1, C78.1, C80.1, C82.1, C83.1, C84.1, C85.1, C86.1, C87.1, C88.1, C89.1, C90.1, C91.1, C92.1, C93.1, C94.1, C95.1, TP15.1, TP17.1, TP19.1, U1.E10 (VCCBRAM), U1.F7 (VCCINT), U1.F9 (VCCINT), U1.F11 (VCCBRAM), U1.G6 (VCCINT), U1.H9 (VCCINT), U1.J6 (VCCINT), U1.K9 (VCCINT), U1.L8 (VCCINT)
+1V8_FPGA: C72.1, C73.1, C75.1, C77.1, C79.1, C81.1, TP13.1, TP14.1, U1.G8 (VCCADC_0), U1.G10 (VCCAUX), U1.J10 (VCCAUX), U1.K11 (VCCAUX), U1.L10 (VCCAUX)
+3V3_FPGA: C109.1, C110.1, C111.1, C112.1, C113.1, C114.1, C115.1, C116.1, C117.1, C118.1, C119.1, C120.1, C121.1, C122.1, C123.1, C124.1, C125.1, C126.1, C127.1, C128.1, C129.1, C130.1, C131.1, C132.1, C133.1, C134.1, C135.1, C136.1, C137.1, C138.1, J1.2, R8.1, R9.1, R10.1, R11.1, R47.1, U1.E7 (CFGBVS_0), U1.L6 (VCCO_0), U1.M9 (M0_0)
CCLK: U1.E8 (CCLK_0)
CONFIG_DONE: R10.2, TP16.1, U1.H10 (DONE_0)
GND: C72.2, C73.2, C74.2, C75.2, C76.2, C77.2, C78.2, C79.2, C80.2, C81.2, C82.2, C83.2, C84.2, C85.2, C86.2, C87.2, C88.2, C89.2, C90.2, C91.2, C92.2, C93.2, C94.2, C95.2, C109.2, C110.2, C111.2, C112.2, C113.2, C114.2, C115.2, C116.2, C117.2, C118.2, C119.2, C120.2, C121.2, C122.2, C123.2, C124.2, C125.2, C126.2, C127.2, C128.2, C129.2, C130.2, C131.2, C132.2, C133.2, C134.2, C135.2, C136.2, C137.2, C138.2, J1.1, J1.3, J1.5, J1.7, J1.9, J1.11, J1.13, SW1.3 (K), SW1.4 (A), U1.A1 (GND), U1.A11 (GND), U1.B8 (GND), U1.C5 (GND), U1.C15 (GND), U1.D2 (GND), U1.D12 (GND), U1.E9 (GND), U1.F6 (GND), U1.F8 (VCCBATT_0), U1.F10 (GND), U1.F16 (GND), U1.G3 (GND), U1.G7 (GNDADC_0), U1.G9 (GND), U1.G13 (GND), U1.H6 (GND), U1.H7 (VREFN_0), U1.H8 (VP_0), U1.J7 (VN_0), U1.J8 (VREFP_0), U1.J9 (GND), U1.J11 (GND), U1.K4 (GND), U1.K6 (GND), U1.K7 (DXN_0), U1.K8 (DXP_0), U1.K14 (GND), U1.L1 (GND), U1.L11 (GND), U1.M8 (GND), U1.M10 (M1_0), U1.M11 (M2_0), U1.N5 (GND), U1.N15 (GND), U1.P2 (GND), U1.P12 (GND), U1.R9 (GND), U1.T6 (GND), U1.T16 (GND), U15.3 (GND), U15.8 (GND)
INIT_B: R47.2, TP1.1, U1.K10 (INIT_B_0)
unnamed: R54.2, SW1.1, SW1.2
PROGRAM_B: R11.2, R54.1, TP18.1, U1.L9 (PROGRAM_B_0)
TCK: J1.6, R9.2, U1.L7 (TCK_0), U15.2 (CH2)
TDI: J1.10, U1.N7 (TDI_0), U15.5 (CH4)
TDO: J1.8, U1.N8 (TDO_0), U15.4 (CH3)
TMS: J1.4, R8.2, U1.M7 (TMS_0), U15.1 (CH1)

Notes on the sheet:
JTAG pullups to avoid floating JTAG with unplugged cable
High CFGBVS_0 means config bank runs at 3.3 V
This is for SRAM
This is for config flash
VCCAUX: 1.8V, 115 mA VCCINT: 1.0V VCCBRAM: 1.0V
JTAG schematics mostly from ug470/pg48
