vgacentrifuge/pcb/centrifuge_combined/fpga_part/vga_input.kicad_sch

## KiCad design centrifuge_combined/fpga_part/vga_input.kicad_sch (2022-10-22)

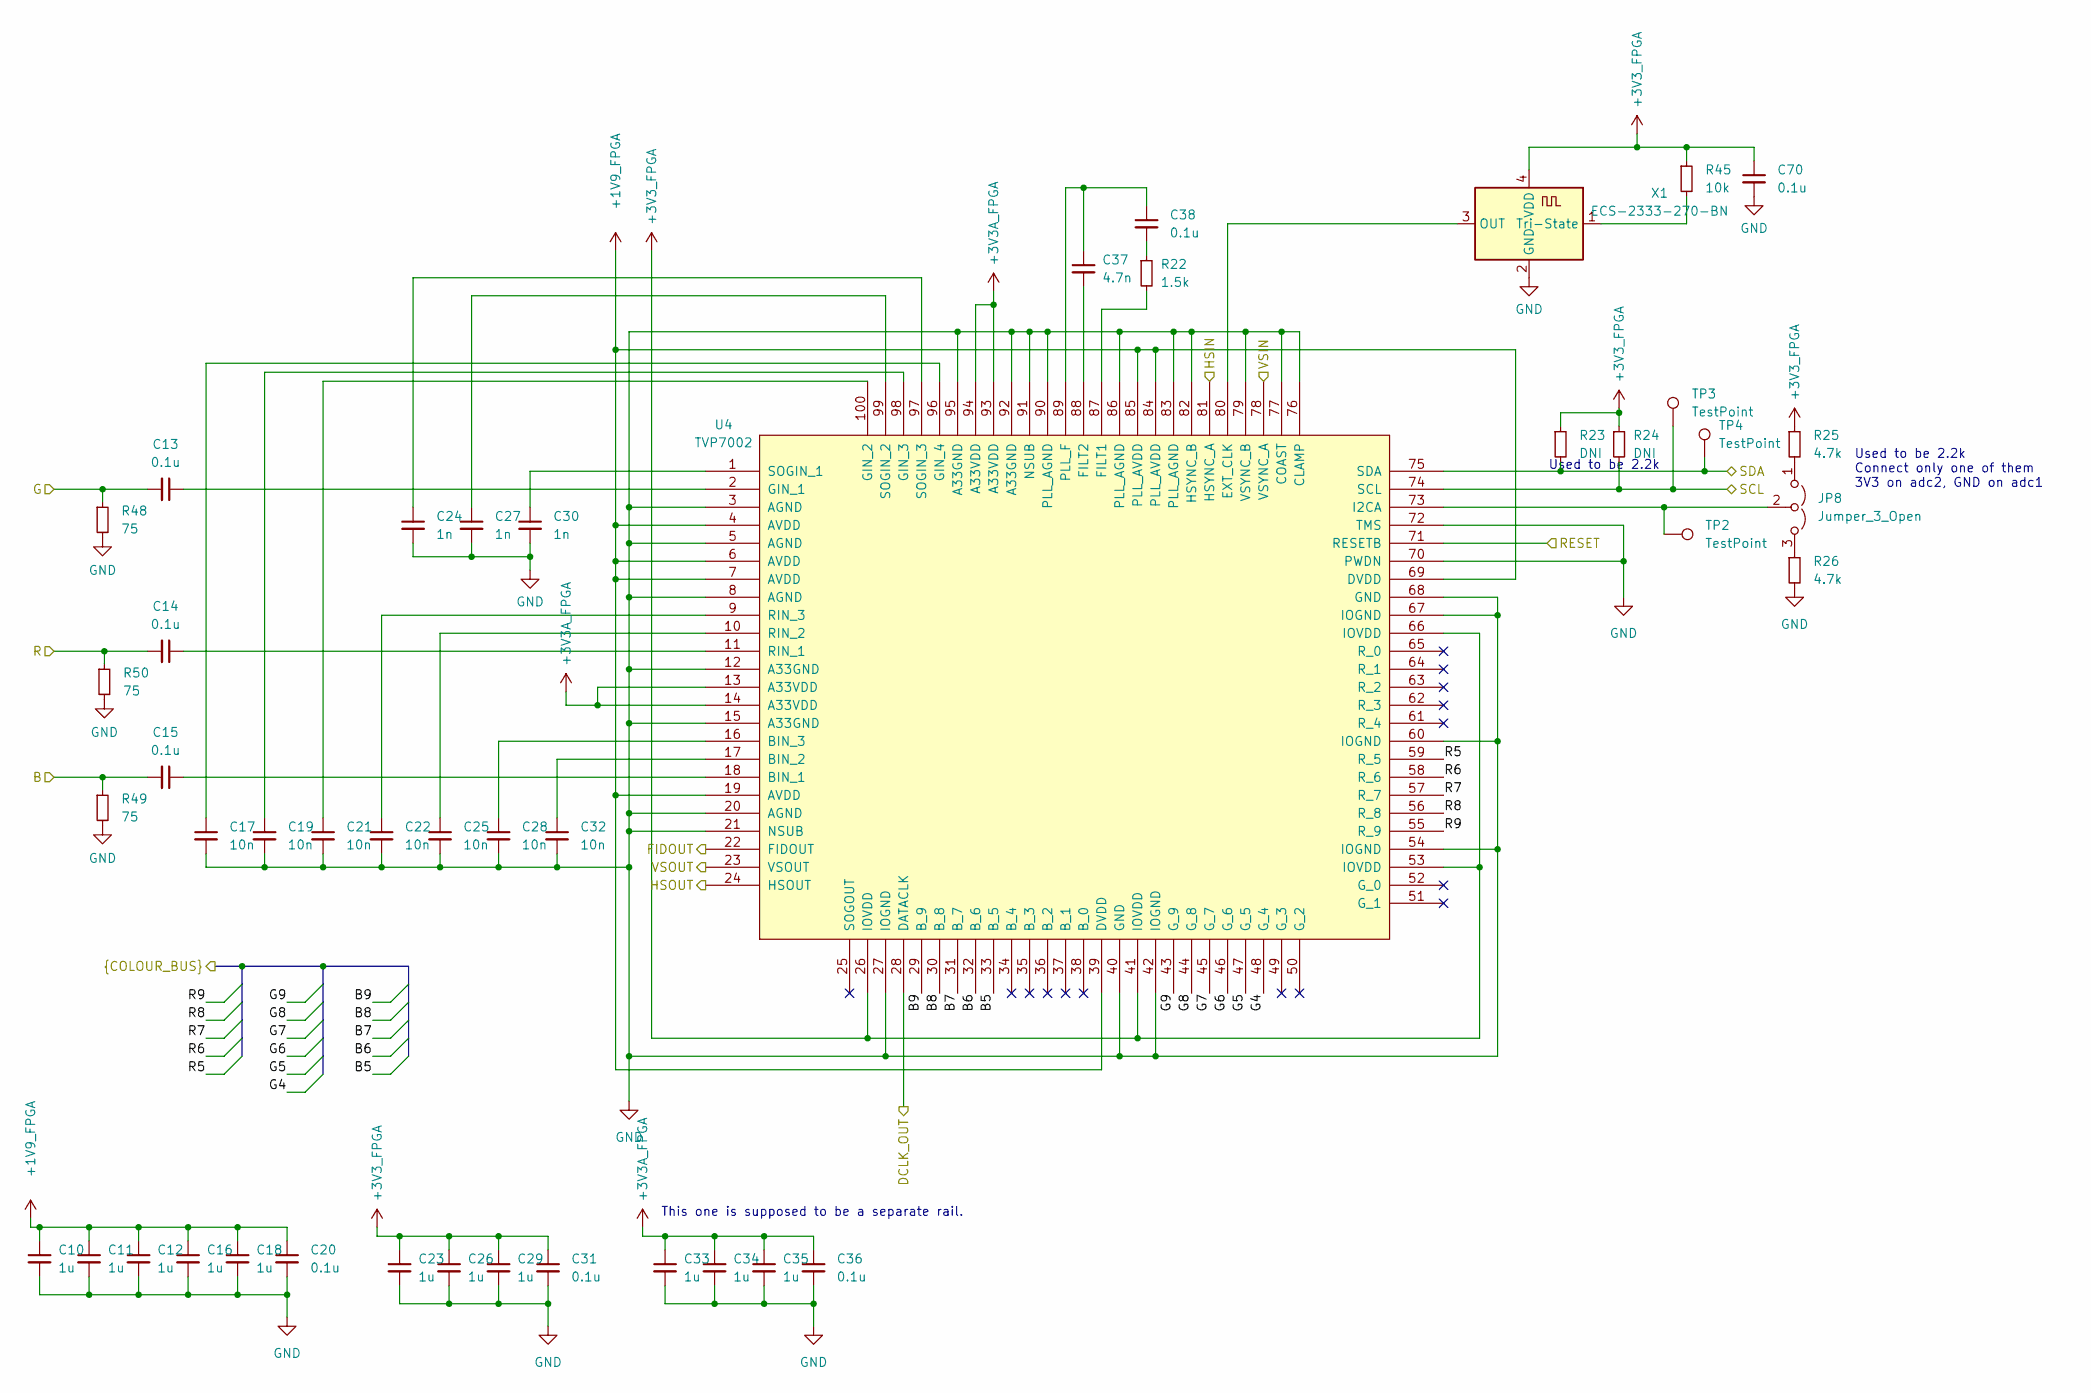
[picture p24: schematic vga_input.kicad_sch]

Parts:
C10, C11, C12, C16, C18, C23, C26, C29, C33, C34, C35: 1u; C_0805_2012Metric_Pad1.18x1.45mm_HandSolder
C13, C14, C15, C20, C31, C36, C38, C70: 0.1u; C_0805_2012Metric_Pad1.18x1.45mm_HandSolder
C17, C19, C21, C22, C25, C28, C32: 10n; C_0805_2012Metric_Pad1.18x1.45mm_HandSolder
C24, C27, C30: 1n; C_0805_2012Metric_Pad1.18x1.45mm_HandSolder
C37: 4.7n; C_0805_2012Metric_Pad1.18x1.45mm_HandSolder
JP8: Jumper_3_Open; SolderJumper-3_P1.3mm_Open_Pad1.0x1.5mm_NumberLabels
R22: 1.5k; R_0805_2012Metric_Pad1.20x1.40mm_HandSolder
R23, R24: DNI; R_0805_2012Metric_Pad1.20x1.40mm_HandSolder
R25, R26: 4.7k; R_0805_2012Metric_Pad1.20x1.40mm_HandSolder
R45: 10k; R_0805_2012Metric_Pad1.20x1.40mm_HandSolder
R48, R49, R50: 75; R_0805_2012Metric_Pad1.20x1.40mm_HandSolder
TP2, TP3, TP4: TestPoint; TestPoint_Keystone_5015_Micro-Minature
U4: TVP7002; TQFP-100-1EP_14x14mm_P0.5mm_EP5x5mm_ThermalVias_elprint
X1: ECS-2333-270-BN; Oscillator_SMD_EuroQuartz_XO32-4Pin_3.2x2.5mm_HandSoldering

Connections:
+1V9_FPGA: C10.1, C11.1, C12.1, C16.1, C18.1, C20.1, U4.4 (AVDD), U4.6 (AVDD), U4.7 (AVDD), U4.19 (AVDD), U4.39 (DVDD), U4.69 (DVDD), U4.84 (PLL_AVDD), U4.85 (PLL_AVDD)
+3V3A_FPGA: C33.1, C34.1, C35.1, C36.1, U4.13 (A33VDD), U4.14 (A33VDD), U4.93 (A33VDD), U4.94 (A33VDD)
+3V3_FPGA: C23.1, C26.1, C29.1, C31.1, C70.1, R23.1, R24.1, R25.1, R45.1, U4.26 (IOVDD), U4.41 (IOVDD), U4.53 (IOVDD), U4.66 (IOVDD), X1.4 (VDD)
B: C15.2, R49.1
B5: U4.33 (B_5)
B6: U4.32 (B_6)
B7: U4.31 (B_7)
B8: U4.30 (B_8)
B9: U4.29 (B_9)
DCLK_OUT: U4.28 (DATACLK)
FIDOUT: U4.22 (FIDOUT)
G: C13.2, R48.1
G4: U4.48 (G_4)
G5: U4.47 (G_5)
G6: U4.46 (G_6)
G7: U4.45 (G_7)
G8: U4.44 (G_8)
G9: U4.43 (G_9)
GND: C10.2, C11.2, C12.2, C16.2, C17.2, C18.2, C19.2, C20.2, C21.2, C22.2, C23.2, C24.2, C25.2, C26.2, C27.2, C28.2, C29.2, C30.2, C31.2, C32.2, C33.2, C34.2, C35.2, C36.2, C70.2, R26.2, R48.2, R49.2, R50.2, U4.3 (AGND), U4.5 (AGND), U4.8 (AGND), U4.12 (A33GND), U4.15 (A33GND), U4.20 (AGND), U4.21 (NSUB), U4.27 (IOGND), U4.40 (GND), U4.42 (IOGND), U4.54 (IOGND), U4.60 (IOGND), U4.67 (IOGND), U4.68 (GND), U4.70 (PWDN), U4.72 (TMS), U4.76 (CLAMP), U4.77 (COAST), U4.79 (VSYNC_B), U4.82 (HSYNC_B), U4.83 (PLL_AGND), U4.86 (PLL_AGND), U4.90 (PLL_AGND), U4.91 (NSUB), U4.92 (A33GND), U4.95 (A33GND), U4.101 (EP_GND), X1.2 (GND)
HSIN: U4.81 (HSYNC_A)
HSOUT: U4.24 (HSOUT)
unnamed: C13.1, U4.2 (GIN_1)
unnamed: C14.1, U4.11 (RIN_1)
unnamed: C15.1, U4.18 (BIN_1)
unnamed: C17.1, U4.96 (GIN_4)
unnamed: C19.1, U4.98 (GIN_3)
unnamed: C21.1, U4.100 (GIN_2)
unnamed: C22.1, U4.9 (RIN_3)
unnamed: C24.1, U4.97 (SOGIN_3)
unnamed: C25.1, U4.10 (RIN_2)
unnamed: C27.1, U4.99 (SOGIN_2)
unnamed: C28.1, U4.16 (BIN_3)
unnamed: C30.1, U4.1 (SOGIN_1)
unnamed: C32.1, U4.17 (BIN_2)
unnamed: C37.1, C38.1, U4.89 (PLL_F)
unnamed: C37.2, U4.88 (FILT2)
unnamed: C38.2, R22.1
unnamed: JP8.1 (A), R25.2
unnamed: JP8.2 (C), TP2.1, U4.73 (I2CA)
unnamed: JP8.3 (B), R26.1
unnamed: R22.2, U4.87 (FILT1)
unnamed: R45.2, X1.1 (Tri-State)
unnamed: U4.80 (EXT_CLK), X1.3 (OUT)
R: C14.2, R50.1
R5: U4.59 (R_5)
R6: U4.58 (R_6)
R7: U4.57 (R_7)
R8: U4.56 (R_8)
R9: U4.55 (R_9)
RESET: U4.71 (RESETB)
SCL: R24.2, TP3.1, U4.74 (SCL)
SDA: R23.2, TP4.1, U4.75 (SDA)
VSIN: U4.78 (VSYNC_A)
VSOUT: U4.23 (VSOUT)

Notes on the sheet:
Used to be 2.2k
Used to be 2.2k Connect only one of them 3V3 on adc2, GND on adc1
This one is supposed to be a separate rail.
