vgacentrifuge/pcb/centrifuge_combined/fpga_part/vga_interface.kicad_sch

## KiCad design centrifuge_combined/fpga_part/vga_interface.kicad_sch (2022-11-12)

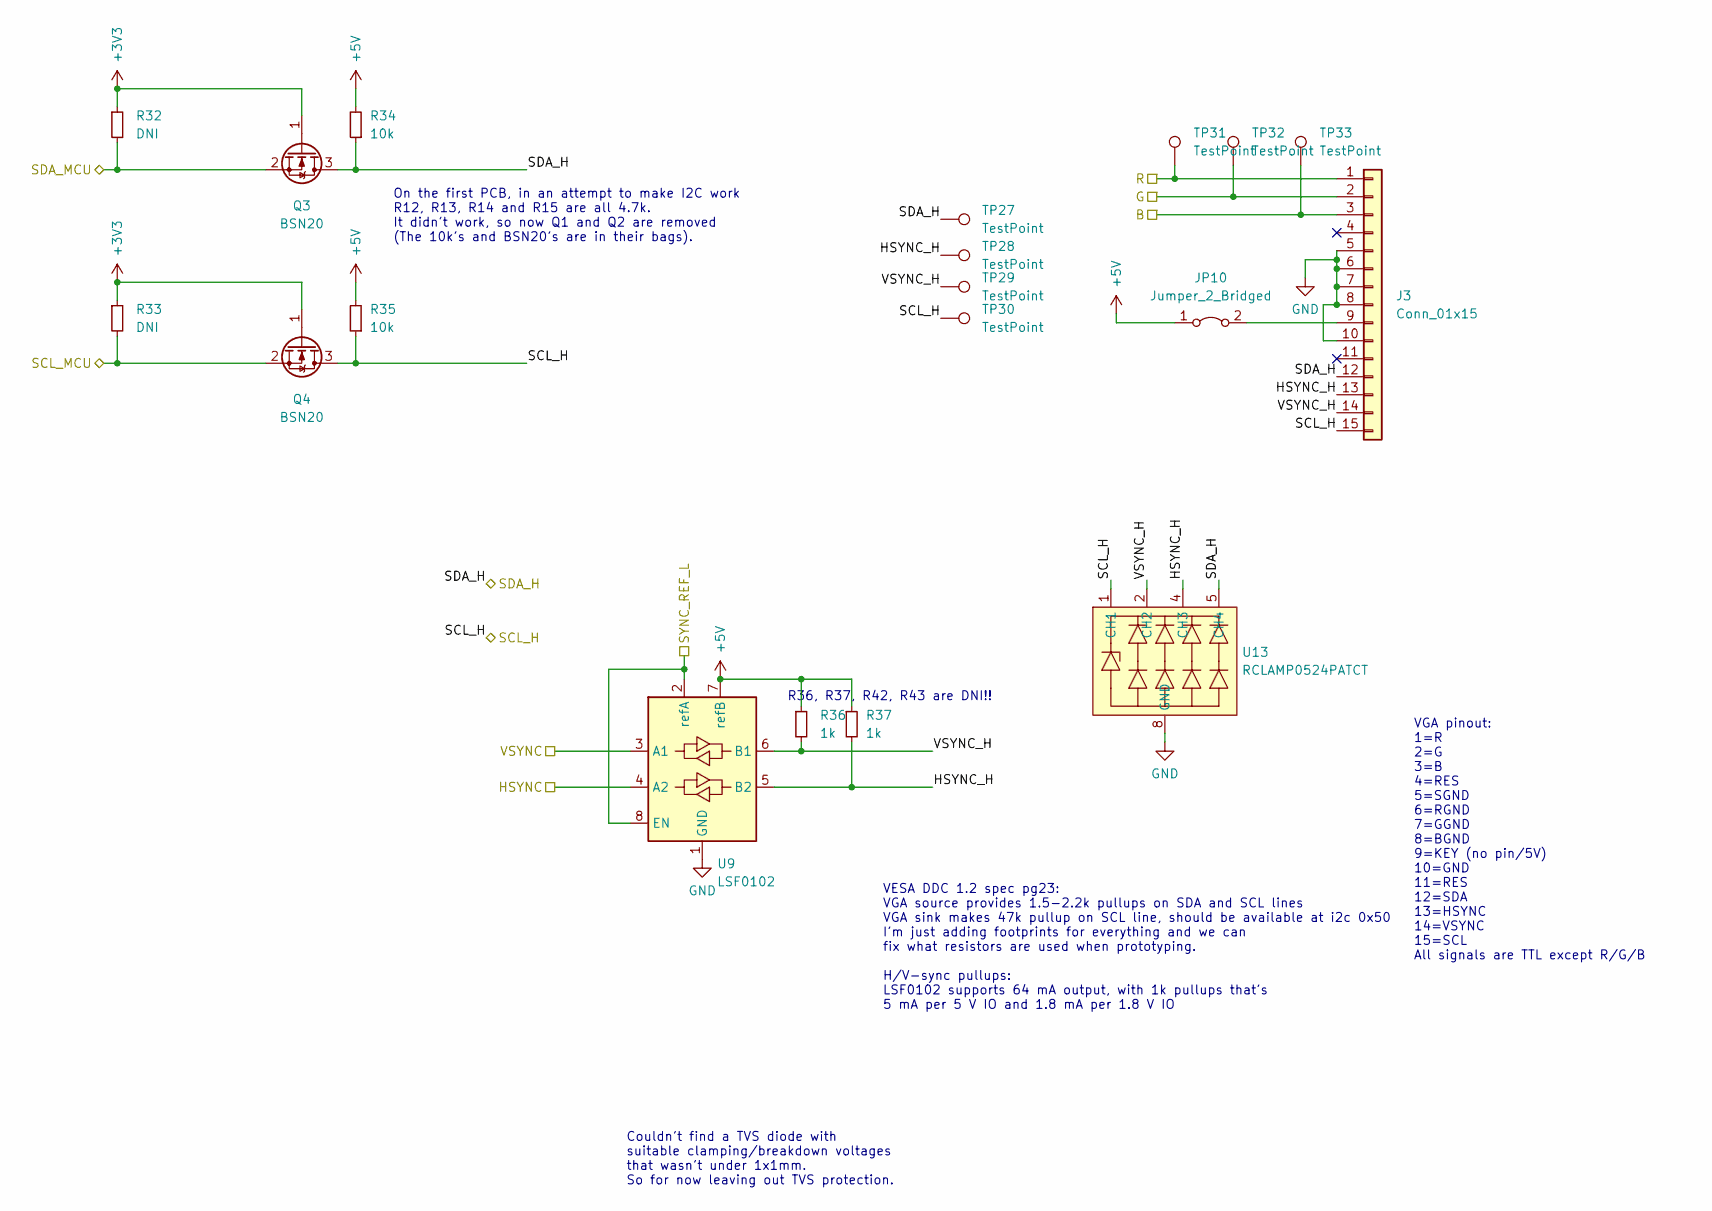
[picture p25: schematic vga_interface.kicad_sch]

Parts:
J3: Conn_01x15; L77HDE15SD1CH4FVGA
JP10: Jumper_2_Bridged; SolderJumper-2_P1.3mm_Bridged_Pad1.0x1.5mm
Q3, Q4: BSN20; SOT-23
R32, R33: DNI; R_0805_2012Metric_Pad1.20x1.40mm_HandSolder
R34, R35: 10k; R_0805_2012Metric_Pad1.20x1.40mm_HandSolder
R36, R37: 1k; R_0805_2012Metric_Pad1.20x1.40mm_HandSolder
TP27, TP28, TP29, TP30, TP31, TP32, TP33: TestPoint; TestPoint_Keystone_5015_Micro-Minature
U9: LSF0102; VSSOP-8_2.3x2mm_P0.5mm
U13: RCLAMP0524PATCT; Diodes_UDFN-10_1.0x2.5mm_P0.5mm

Connections:
+3V3: Q3.1 (G), Q4.1 (G), R32.1, R33.1
+5V: JP10.1 (A), R34.2, R35.2, R36.1, R37.1, U9.7 (refB)
B: J3.3, TP33.1
G: J3.2, TP32.1
GND: J3.5, J3.6, J3.7, J3.8, J3.10, U9.1 (GND), U13.3 (GND), U13.8 (GND)
HSYNC: U9.4 (A2)
HSYNC_H: J3.13, R37.2, TP28.1, U9.5 (B2), U13.4 (CH3)
unnamed: J3.9, JP10.2 (B)
R: J3.1, TP31.1
SCL_H: J3.15, Q4.3 (D), R35.1, TP30.1, U13.1 (CH1)
SCL_MCU: Q4.2 (S), R33.2
SDA_H: J3.12, Q3.3 (D), R34.1, TP27.1, U13.5 (CH4)
SDA_MCU: Q3.2 (S), R32.2
SYNC_REF_L: U9.2 (refA), U9.8 (EN)
VSYNC: U9.3 (A1)
VSYNC_H: J3.14, R36.2, TP29.1, U9.6 (B1), U13.2 (CH2)

Notes on the sheet:
On the first PCB, in an attempt to make I2C work R12, R13, R14 and R15 are all 4.7k. It didn't work, so now Q1 and Q2 are removed (The 10k's and BSN20's are in their bags).
Couldn't find a TVS diode with suitable clamping/breakdown voltages that wasn't under 1x1mm. So for now leaving out TVS protection.
VGA pinout: 1=R 2=G 3=B 4=RES 5=SGND 6=RGND 7=GGND 8=BGND 9=KEY (no pin/5V) 10=GND 11=RES 12=SDA 13=HSYNC 14=VSYNC 15=SCL All signals are TTL except R/G/B
R36, R37, R42, R43 are DNI!!
VESA DDC 1.2 spec pg23: VGA source provides 1.5-2.2k pullups on SDA and SCL lines VGA sink makes 47k pullup on SCL line, should be available at i2c 0x50 I'm just adding footprints for everything and we can fix what resistors are used when prototyping. H/V-sync pullups: LSF0102 supports 64 mA output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
