vgacentrifuge/pcb/centrifuge_combined/fpga_part/vga_output.kicad_sch

## KiCad design centrifuge_combined/fpga_part/vga_output.kicad_sch (2022-10-22)

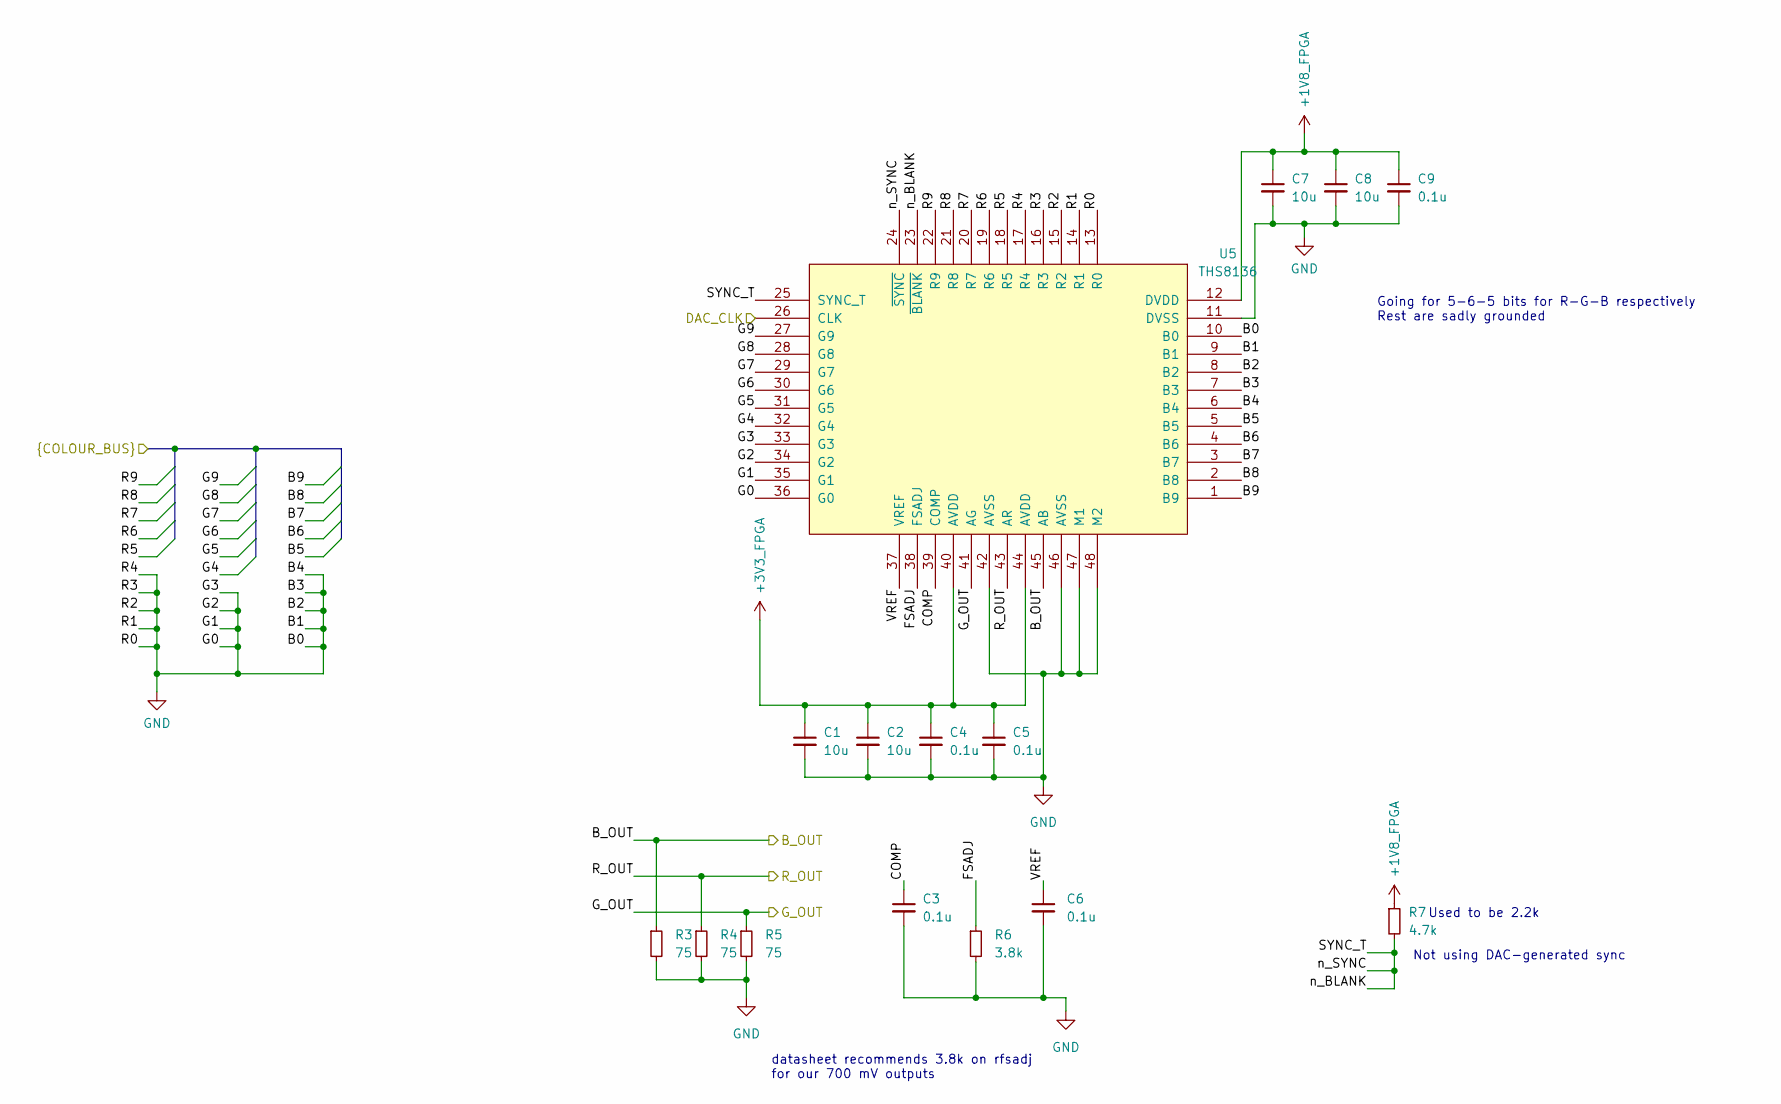
[picture p26: schematic vga_output.kicad_sch]

Parts:
C1, C2, C7, C8: 10u; C_0805_2012Metric_Pad1.18x1.45mm_HandSolder
C3, C4, C5, C6, C9: 0.1u; C_0805_2012Metric_Pad1.18x1.45mm_HandSolder
R3, R4, R5: 75; R_0805_2012Metric_Pad1.20x1.40mm_HandSolder
R6: 3.8k; R_0805_2012Metric_Pad1.20x1.40mm_HandSolder
R7: 4.7k; R_0805_2012Metric_Pad1.20x1.40mm_HandSolder
U5: THS8136; LQFP-48-1EP_7x7mm_P0.5mm_EP3.6x3.6mm

Connections:
+1V8_FPGA: C7.1, C8.1, C9.1, R7.1, U5.12 (DVDD)
+3V3_FPGA: C1.1, C2.1, C4.1, C5.1, U5.40 (AVDD), U5.44 (AVDD)
B5: U5.5 (B5)
B6: U5.4 (B6)
B7: U5.3 (B7)
B8: U5.2 (B8)
B9: U5.1 (B9)
B_OUT: R3.1, U5.45 (AB)
COMP: C3.1, U5.39 (COMP)
DAC_CLK: U5.26 (CLK)
FSADJ: R6.1, U5.38 (FSADJ)
G4: U5.32 (G4)
G5: U5.31 (G5)
G6: U5.30 (G6)
G7: U5.29 (G7)
G8: U5.28 (G8)
G9: U5.27 (G9)
GND: C1.2, C2.2, C3.2, C4.2, C5.2, C6.2, C7.2, C8.2, C9.2, R3.2, R4.2, R5.2, R6.2, U5.6 (B4), U5.7 (B3), U5.8 (B2), U5.9 (B1), U5.10 (B0), U5.11 (DVSS), U5.13 (R0), U5.14 (R1), U5.15 (R2), U5.16 (R3), U5.17 (R4), U5.33 (G3), U5.34 (G2), U5.35 (G1), U5.36 (G0), U5.42 (AVSS), U5.46 (AVSS), U5.47 (M1), U5.48 (M2), U5.49 (THERMAL)
G_OUT: R5.1, U5.41 (AG)
R5: U5.18 (R5)
R6: U5.19 (R6)
R7: U5.20 (R7)
R8: U5.21 (R8)
R9: U5.22 (R9)
R_OUT: R4.1, U5.43 (AR)
VREF: C6.1, U5.37 (VREF)
n_BLANK: R7.2, U5.23 (~BLANK), U5.24 (~SYNC), U5.25 (SYNC_T)

Notes on the sheet:
Used to be 2.2k
datasheet recommends 3.8k on rfsadj for our 700 mV outputs
Going for 5-6-5 bits for R-G-B respectively Rest are sadly grounded
Not using DAC-generated sync
