vgacentrifuge/pcb/centrifuge_combined/mcu_part/SD_card.kicad_sch

## KiCad design centrifuge_combined/mcu_part/SD_card.kicad_sch (2022-10-04)

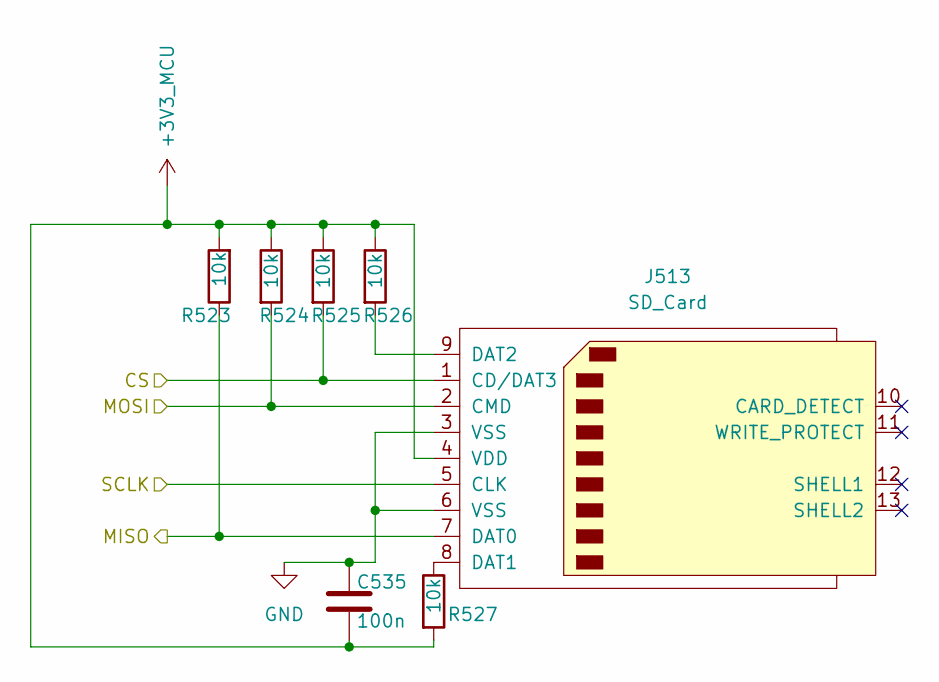
[picture p27: schematic SD_card.kicad_sch]

Parts:
C535: 100n; C_0805_2012Metric_Pad1.18x1.45mm_HandSolder
J513: SD_Card; SD_Kyocera_145638009511859+
R523, R524, R525, R526, R527: 10k; R_0805_2012Metric_Pad1.20x1.40mm_HandSolder

Connections:
+3V3_MCU: C535.2, J513.4 (VDD), R523.2, R524.1, R525.1, R526.1, R527.2
CS: J513.1 (CD/DAT3), R525.2
GND: C535.1, J513.3 (VSS), J513.6 (VSS)
MISO: J513.7 (DAT0), R523.1
MOSI: J513.2 (CMD), R524.2
unnamed: J513.8 (DAT1), R527.1
unnamed: J513.9 (DAT2), R526.2
SCLK: J513.5 (CLK)
