vgacentrifuge/pcb/centrifuge_combined/mcu_part/button_panel.kicad_sch

## KiCad design centrifuge_combined/mcu_part/button_panel.kicad_sch (2022-10-22)

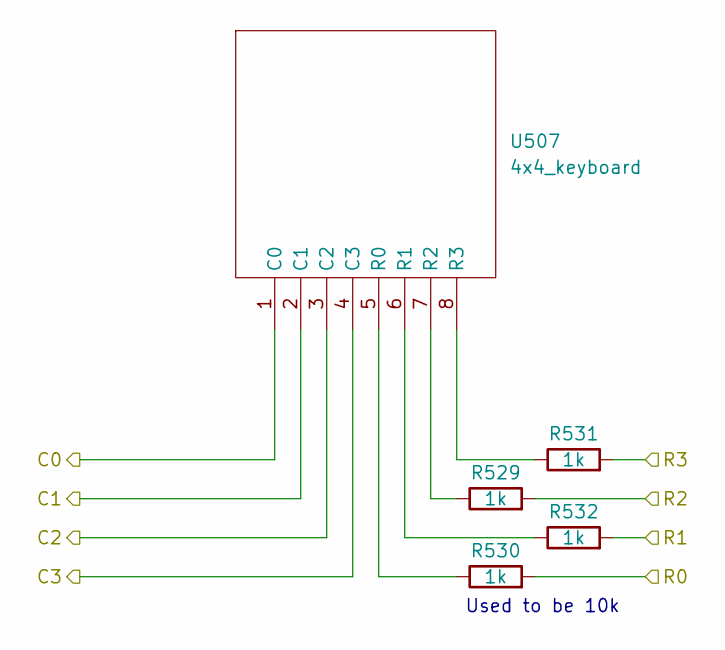
[picture p28: schematic button_panel.kicad_sch]

Parts:
R529, R530, R531, R532: 1k; R_0805_2012Metric_Pad1.20x1.40mm_HandSolder
U507: 4x4_keyboard; Adafruit 3844

Connections:
C0: U507.1 (C0)
C1: U507.2 (C1)
C2: U507.3 (C2)
C3: U507.4 (C3)
unnamed: R529.1, U507.7 (R2)
unnamed: R530.1, U507.5 (R0)
unnamed: R531.1, U507.8 (R3)
unnamed: R532.1, U507.6 (R1)
R0: R530.2
R1: R532.2
R2: R529.2
R3: R531.2

Notes on the sheet:
Used to be 10k
