vgacentrifuge/pcb/centrifuge_combined/mcu_part/centrifuge_mcu.kicad_sch

## KiCad design centrifuge_combined/mcu_part/centrifuge_mcu.kicad_sch (2022-10-28)

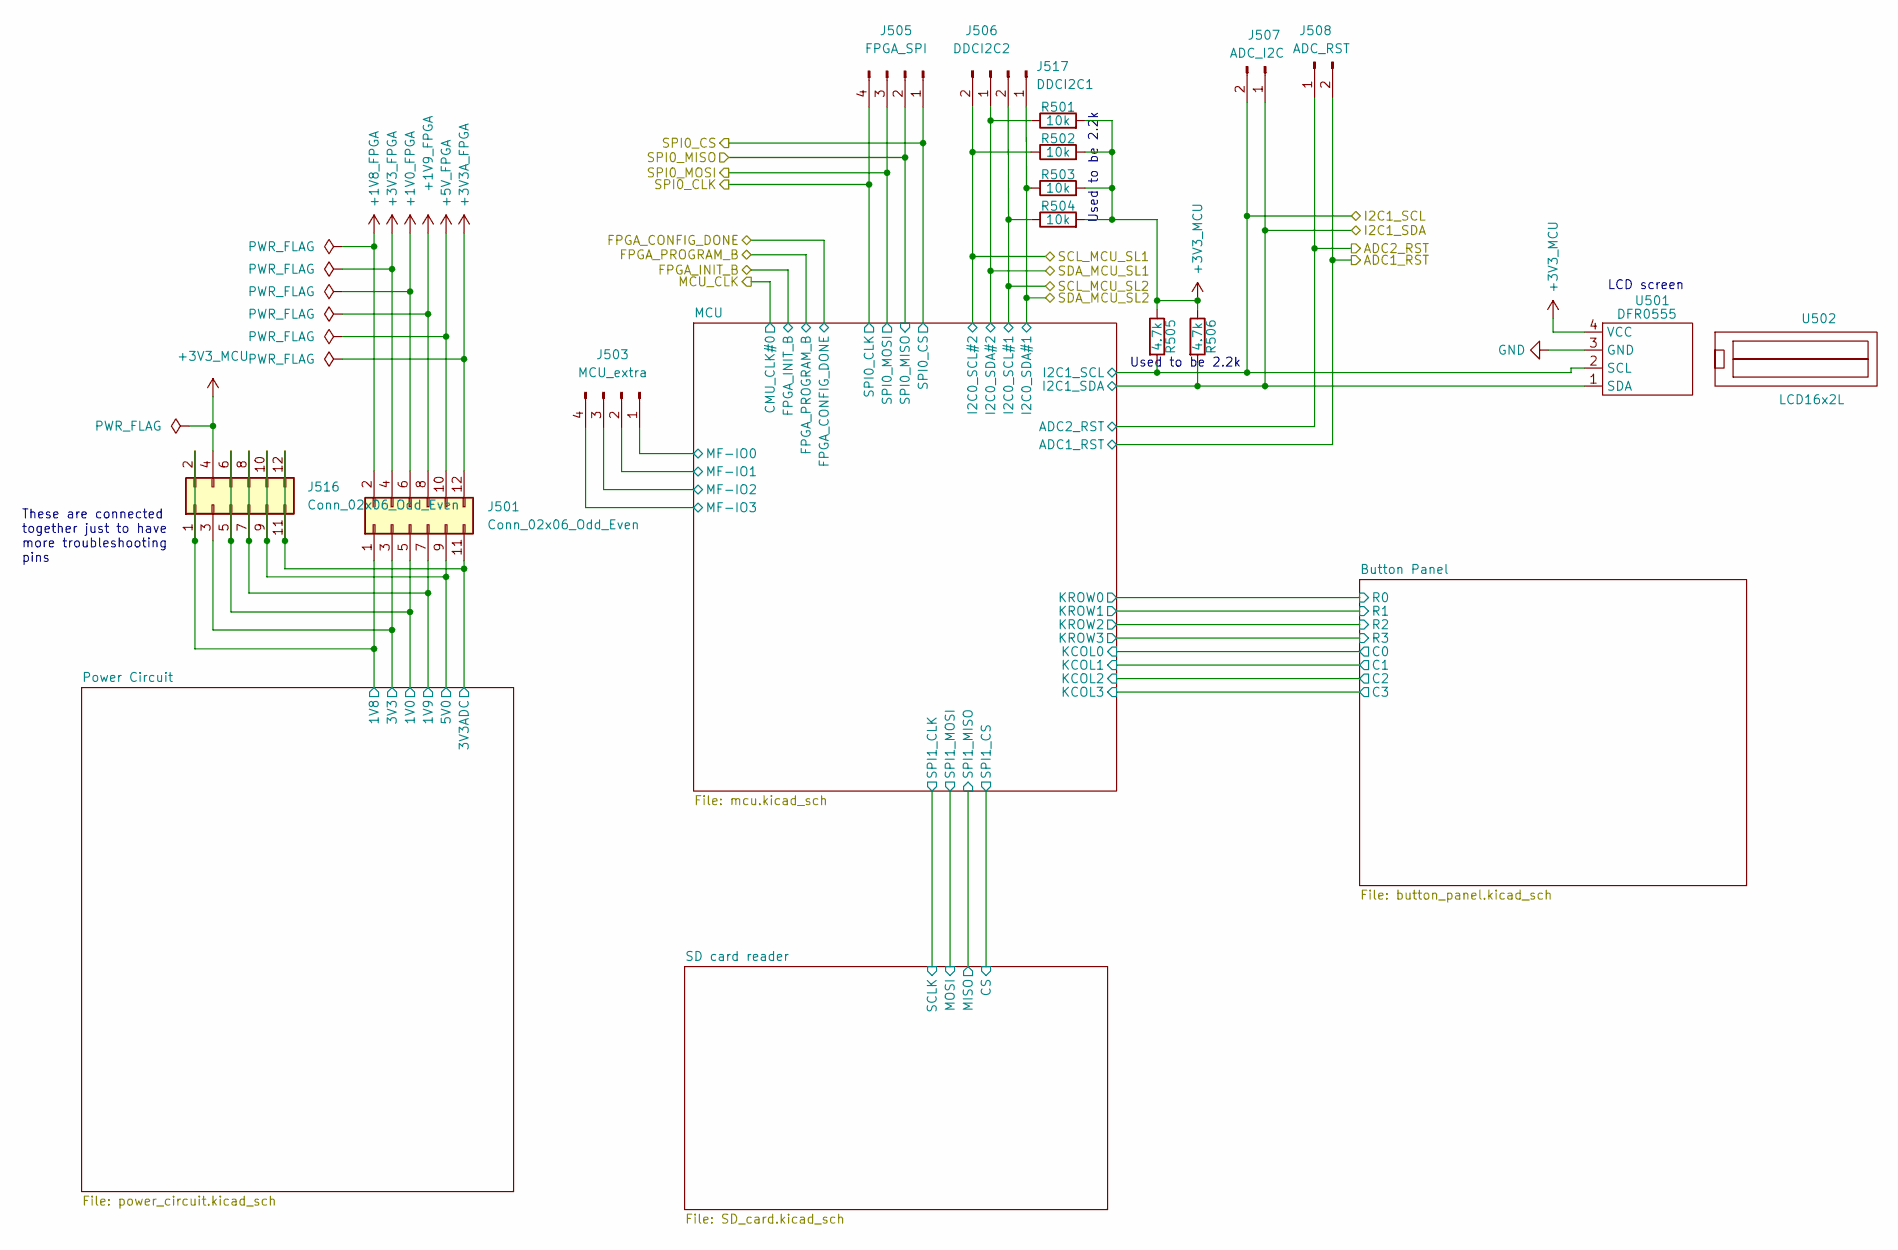
[picture p29: schematic centrifuge_mcu.kicad_sch]

Parts:
J501, J516: Conn_02x06_Odd_Even; PinHeader_2x06_P2.54mm_Vertical
J503: MCU_extra; PinHeader_1x04_P2.54mm_Vertical
J505: FPGA_SPI; PinHeader_1x04_P2.54mm_Vertical
J506: DDCI2C2; PinHeader_1x02_P2.54mm_Vertical
J507: ADC_I2C; PinHeader_1x02_P2.54mm_Vertical
J508: ADC_RST; PinHeader_1x02_P2.54mm_Vertical
J517: DDCI2C1; PinHeader_1x02_P2.54mm_Vertical
R501, R502, R503, R504: 10k; R_0805_2012Metric_Pad1.20x1.40mm_HandSolder
R505, R506: 4.7k; R_0805_2012Metric_Pad1.20x1.40mm_HandSolder
U501: DFR0555; PinHeader_1x04_P2.54mm_Vertical
U502: LCD16x2L; DFR0555

Connections:
1V0: J501.5, J516.5, J516.6
1V8: J501.1, J516.1, J516.2
1V9: J501.7, J516.7, J516.8
3V3: J501.3, J516.3
3V3ADC: J501.11, J516.11, J516.12
5V0: J501.9, J516.9, J516.10
+1V0_FPGA: J501.6
+1V8_FPGA: J501.2
+1V9_FPGA: J501.8
+3V3A_FPGA: J501.12
+3V3_FPGA: J501.4
+3V3_MCU: J516.4, R501.2, R502.2, R503.2, R504.2, R505.1, R506.1, U501.4 (VCC)
+5V_FPGA: J501.10
ADC1_RST: J508.2
ADC2_RST: J508.1
GND: U501.3 (GND)
I2C1_SCL: J507.2, R505.2, U501.2 (SCL)
I2C1_SDA: J507.1, R506.2, U501.1 (SDA)
MF-IO0: J503.1
MF-IO1: J503.2
MF-IO2: J503.3
MF-IO3: J503.4
SCL_MCU_SL1: J506.2, R502.1
SCL_MCU_SL2: J517.2, R504.1
SDA_MCU_SL1: J506.1, R501.1
SDA_MCU_SL2: J517.1, R503.1
SPI0_CLK: J505.4
SPI0_CS: J505.1
SPI0_MISO: J505.2
SPI0_MOSI: J505.3

Notes on the sheet:
Used to be 2.2k
LCD screen
These are connected together just to have more troubleshooting pins
