vgacentrifuge/pcb/centrifuge_combined/mcu_part/mcu.kicad_sch

## KiCad design centrifuge_combined/mcu_part/mcu.kicad_sch (2022-10-28)

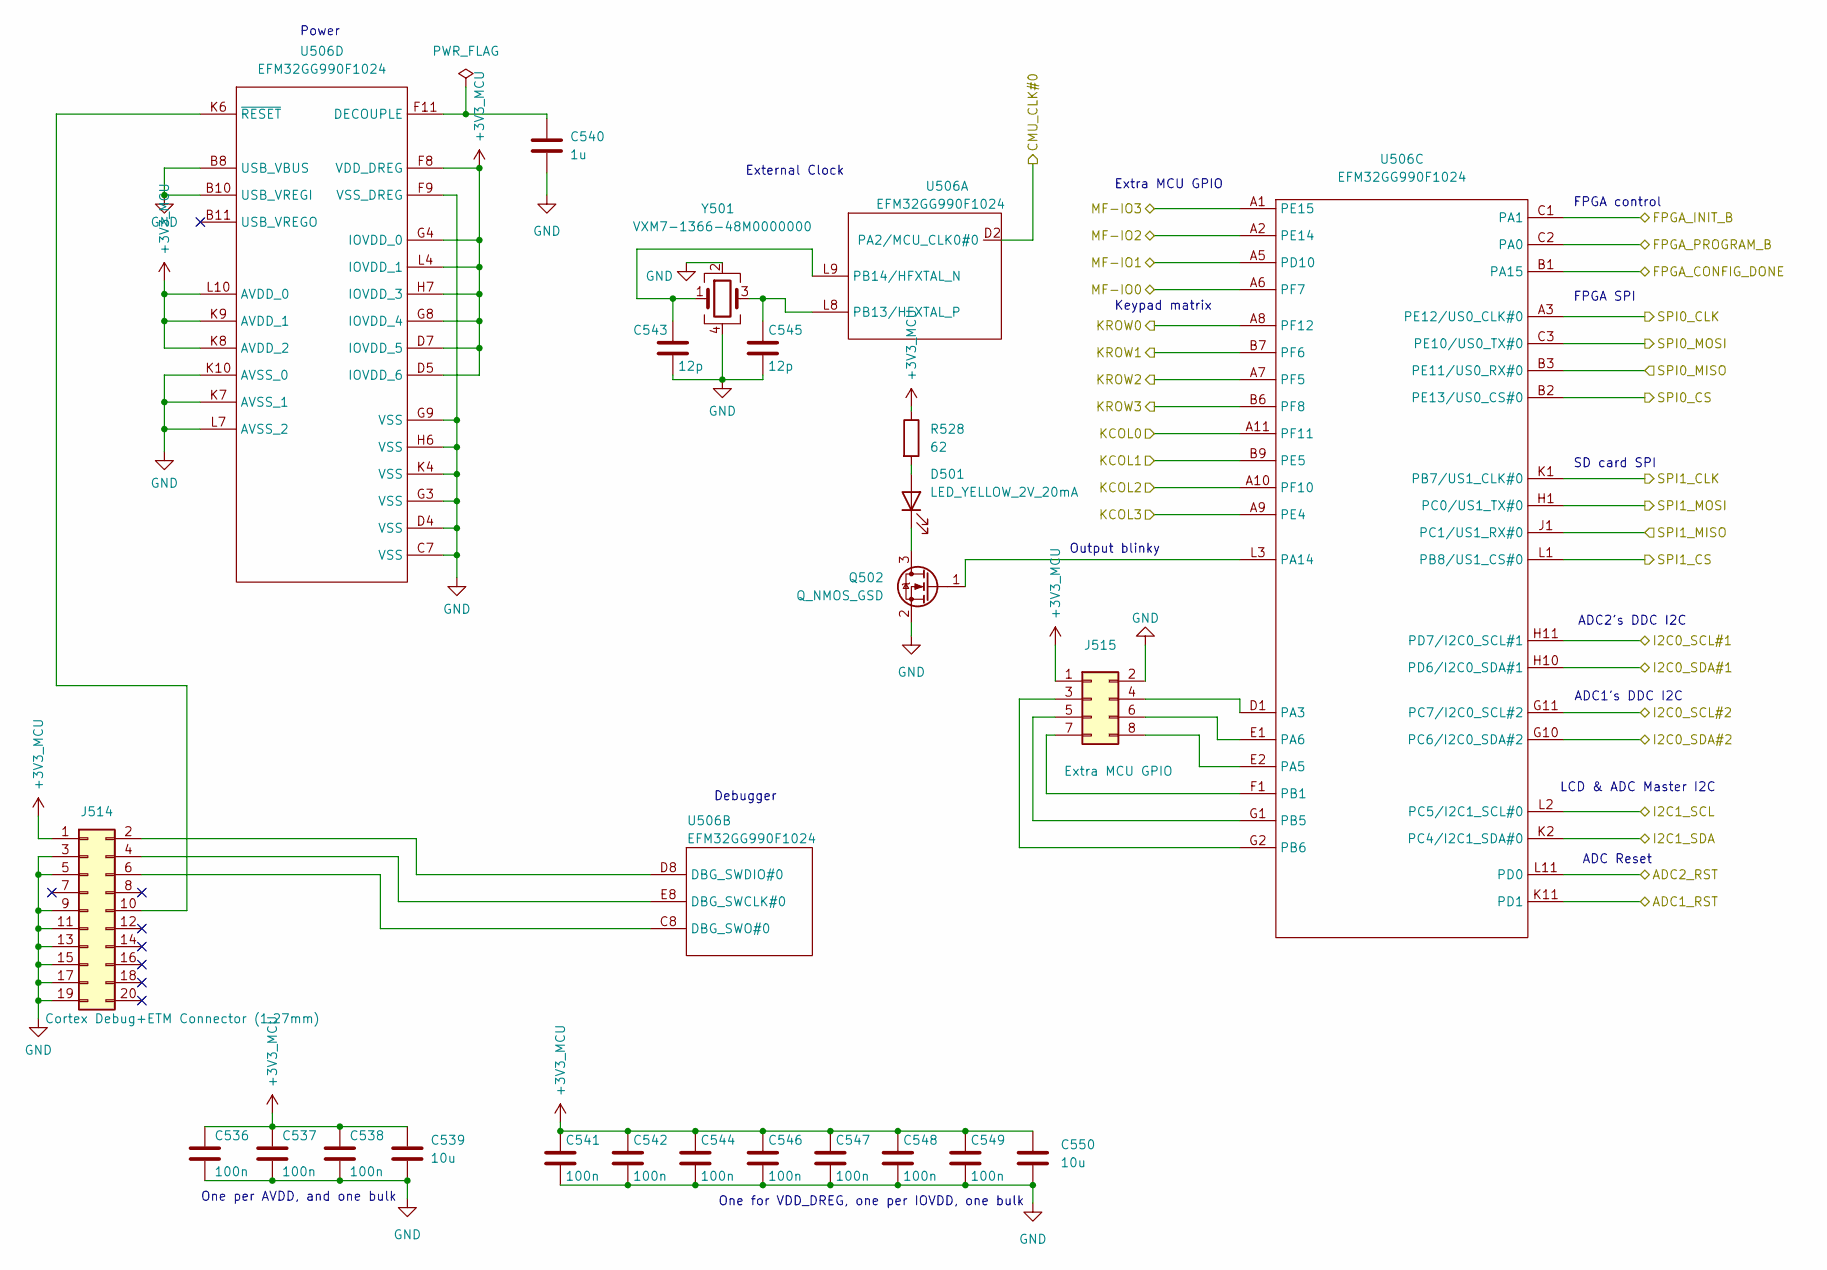
[picture p30: schematic mcu.kicad_sch]

Parts:
C536, C537, C538, C541, C542, C544, C546, C547, C548, C549: 100n; C_0805_2012Metric_Pad1.18x1.45mm_HandSolder
C539, C550: 10u; C_0805_2012Metric_Pad1.18x1.45mm_HandSolder
C540: 1u; C_0805_2012Metric_Pad1.18x1.45mm_HandSolder
C543, C545: 12p; C_0805_2012Metric_Pad1.18x1.45mm_HandSolder
D501: LED_YELLOW_2V_20mA; D_0805_2012Metric_Pad1.15x1.40mm_HandSolder
J514: DEBUG; PinHeader_2x10_P1.27mm_Vertical
J515: Extra MCU GPIO; PinHeader_2x04_P2.54mm_Vertical
Q502: Q_NMOS_GSD; SOT-323_SC-70_Handsoldering
R528: 62; R_0805_2012Metric_Pad1.20x1.40mm_HandSolder
U506: EFM32GG990F1024; BGA-112_9.0x9.0mm_Layout11x11_P0.8mm_Ball0.4mm_Pad0.35mm_NS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
Y501: VXM7-1366-48M0000000; Crystal_SMD_TXC_7M-4Pin_3.2x2.5mm_TIGHT

Connections:
+3V3_MCU: C536.1, C537.1, C538.1, C539.1, C541.1, C542.1, C544.1, C546.1, C547.1, C548.1, C549.1, C550.1, J514.1, J515.1, R528.1, U506.D5 (IOVDD_6), U506.D7 (IOVDD_5), U506.F8 (VDD_DREG), U506.G4 (IOVDD_0), U506.G8 (IOVDD_4), U506.H7 (IOVDD_3), U506.K8 (AVDD_2), U506.K9 (AVDD_1), U506.L4 (IOVDD_1), U506.L10 (AVDD_0)
ADC1_RST: U506.K11 (PD1)
ADC2_RST: U506.L11 (PD0)
CMU_CLK#0: U506.D2 (PA2/MCU_CLK0#0)
FPGA_CONFIG_DONE: U506.B1 (PA15)
FPGA_INIT_B: U506.C1 (PA1)
FPGA_PROGRAM_B: U506.C2 (PA0)
GND: C536.2, C537.2, C538.2, C539.2, C540.1, C541.2, C542.2, C543.2, C544.2, C545.2, C546.2, C547.2, C548.2, C549.2, C550.2, J514.3, J514.5, J514.9, J514.11, J514.13, J514.15, J514.17, J514.19, J515.2, Q502.2 (S), U506.B8 (USB_VBUS), U506.B10 (USB_VREGI), U506.C7 (VSS), U506.D4 (VSS), U506.F9 (VSS_DREG), U506.G3 (VSS), U506.G9 (VSS), U506.H6 (VSS), U506.K4 (VSS), U506.K7 (AVSS_1), U506.K10 (AVSS_0), U506.L7 (AVSS_2), Y501.2, Y501.4
I2C0_SCL#1: U506.H11 (PD7/I2C0_SCL#1)
I2C0_SCL#2: U506.G11 (PC7/I2C0_SCL#2)
I2C0_SDA#1: U506.H10 (PD6/I2C0_SDA#1)
I2C0_SDA#2: U506.G10 (PC6/I2C0_SDA#2)
I2C1_SCL: U506.L2 (PC5/I2C1_SCL#0)
I2C1_SDA: U506.K2 (PC4/I2C1_SDA#0)
KCOL0: U506.A11 (PF11)
KCOL1: U506.B9 (PE5)
KCOL2: U506.A10 (PF10)
KCOL3: U506.A9 (PE4)
KROW0: U506.A8 (PF12)
KROW1: U506.B7 (PF6)
KROW2: U506.A7 (PF5)
KROW3: U506.B6 (PF8)
MF-IO0: U506.A6 (PF7)
MF-IO1: U506.A5 (PD10)
MF-IO2: U506.A2 (PE14)
MF-IO3: U506.A1 (PE15)
unnamed: C540.2, U506.F11 (DECOUPLE)
unnamed: C543.1, U506.L9 (PB14/HFXTAL_N), Y501.1
unnamed: C545.1, U506.L8 (PB13/HFXTAL_P), Y501.3
unnamed: D501.1 (K), Q502.3 (D)
unnamed: D501.2 (A), R528.2
unnamed: J514.2, U506.D8 (DBG_SWDIO#0)
unnamed: J514.4, U506.E8 (DBG_SWCLK#0)
unnamed: J514.6, U506.C8 (DBG_SWO#0)
unnamed: J514.10, U506.K6 (~RESET)
unnamed: J515.3, U506.G2 (PB6)
unnamed: J515.4, U506.D1 (PA3)
unnamed: J515.5, U506.G1 (PB5)
unnamed: J515.6, U506.E1 (PA6)
unnamed: J515.7, U506.F1 (PB1)
unnamed: J515.8, U506.E2 (PA5)
unnamed: Q502.1 (G), U506.L3 (PA14)
SPI0_CLK: U506.A3 (PE12/US0_CLK#0)
SPI0_CS: U506.B2 (PE13/US0_CS#0)
SPI0_MISO: U506.B3 (PE11/US0_RX#0)
SPI0_MOSI: U506.C3 (PE10/US0_TX#0)
SPI1_CLK: U506.K1 (PB7/US1_CLK#0)
SPI1_CS: U506.L1 (PB8/US1_CS#0)
SPI1_MISO: U506.J1 (PC1/US1_RX#0)
SPI1_MOSI: U506.H1 (PC0/US1_TX#0)

Notes on the sheet:
External Clock
Extra MCU GPIO
Keypad matrix
FPGA SPI
Debugger
Output blinky
SD card SPI
One per AVDD, and one bulk
ADC2's DDC I2C
LCD & ADC Master I2C
ADC Reset
One for VDD_DREG, one per IOVDD, one bulk
FPGA control
Power
ADC1's DDC I2C
