vgacentrifuge/pcb/centrifuge_combined/mcu_part/power_circuit.kicad_sch

## KiCad design centrifuge_combined/mcu_part/power_circuit.kicad_sch (2022-10-28)

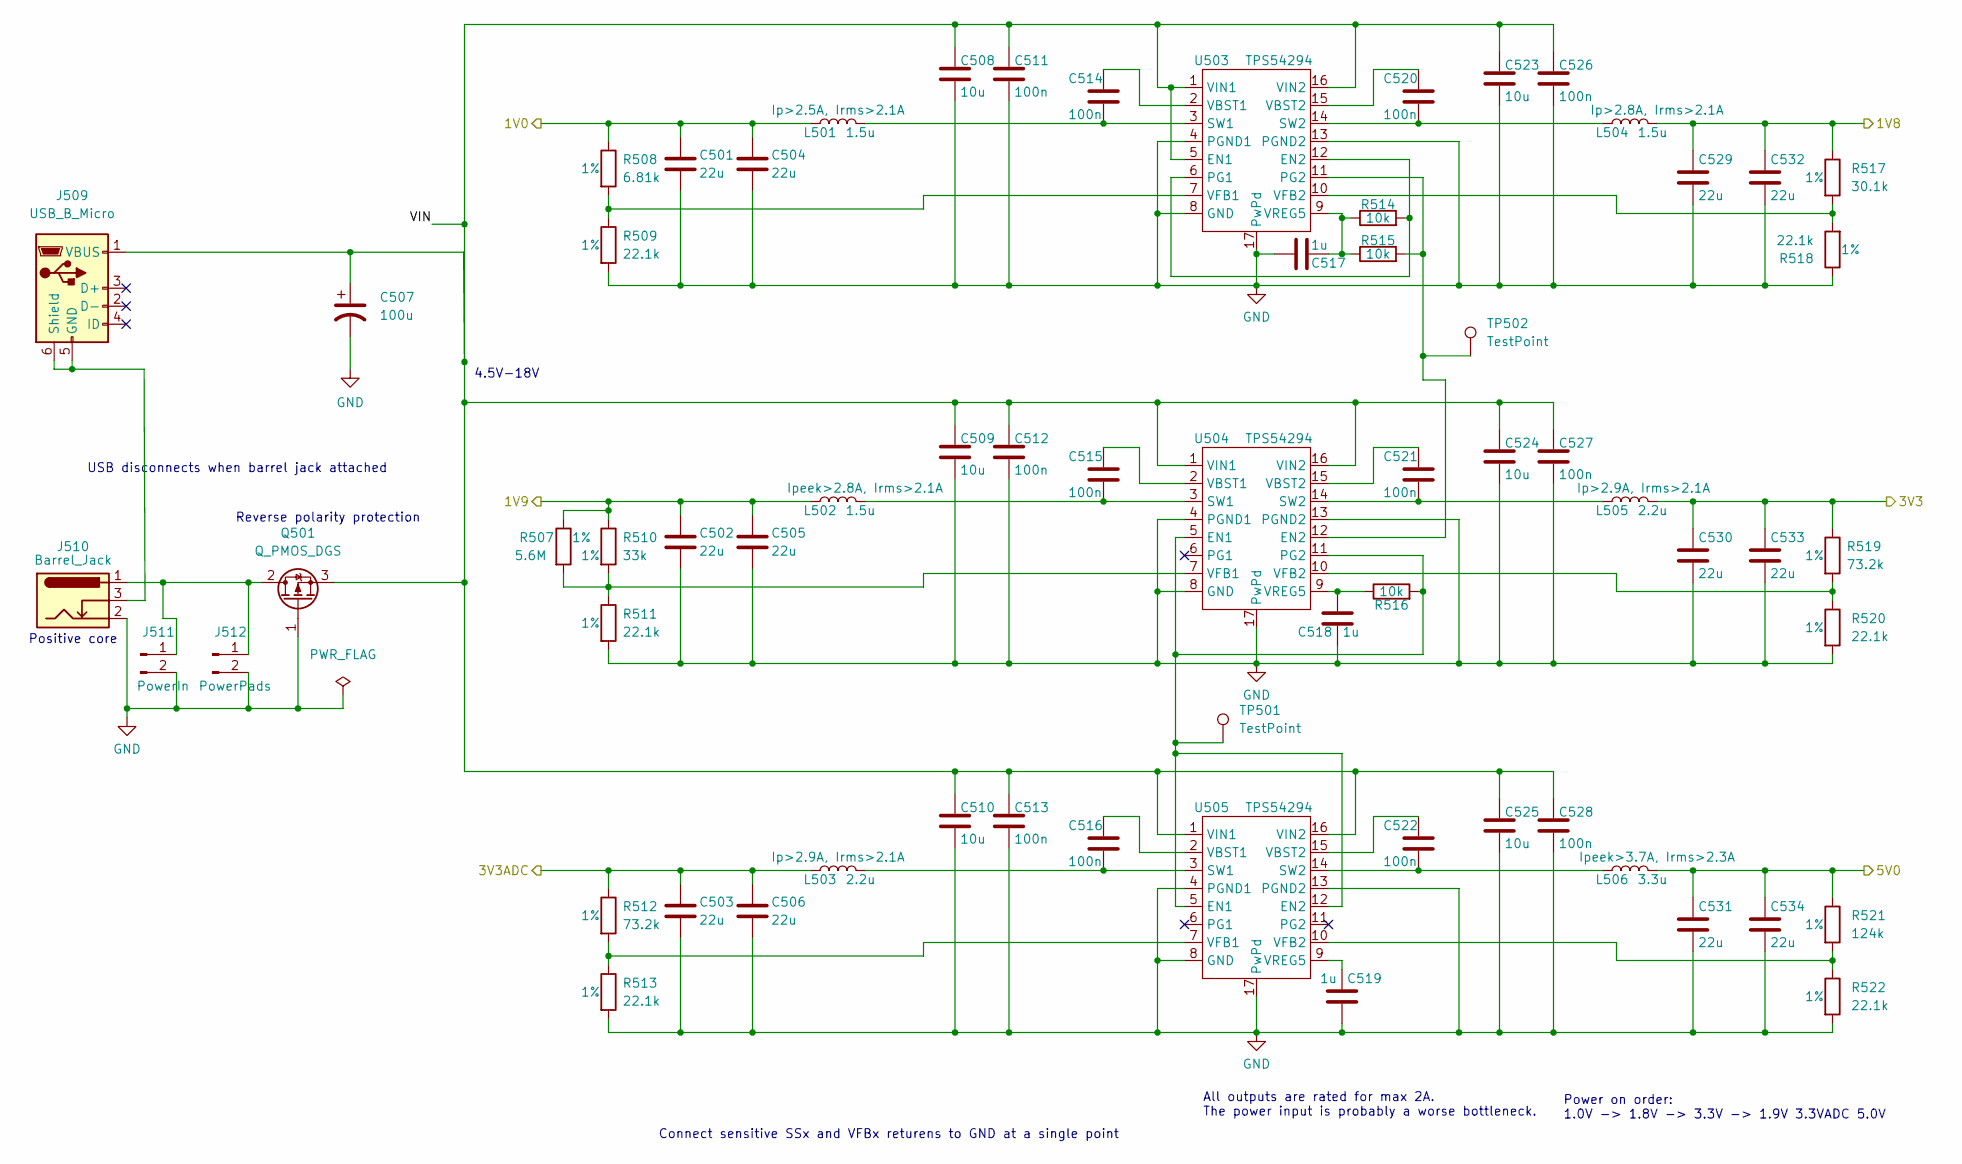
[picture p31: schematic power_circuit.kicad_sch]

Parts:
C501, C502, C503, C504, C505, C506, C529, C530, C531, C532, C533, C534: 22u; C_1206_3216Metric_Pad1.33x1.80mm_HandSolder
C507: 100u; CP_Radial_D10.0mm_P5.00mm
C508, C509, C510, C523, C524, C525: 10u; C_1206_3216Metric_Pad1.33x1.80mm_HandSolder
C511, C512, C513, C514, C515, C516, C520, C521, C522, C526, C527, C528: 100n; C_1206_3216Metric_Pad1.33x1.80mm_HandSolder
C517, C518, C519: 1u; C_0805_2012Metric_Pad1.18x1.45mm_HandSolder
J509: USB_B_Micro; USB_Micro-B_Molex-105017-0001
J510: Barrel_Jack; BarrelJack_CUI_PJ-102AH_Horizontal
J511: PowerIn; PinHeader_1x02_P2.54mm_Vertical
J512: PowerPads
L501: 1.5u; L_Sumida_CR75; Tolerance Ip>2.5A, Irms>2.1A
L502: 1.5u; L_Sumida_CR75; Tolerance Ipeek>2.8A, Irms>2.1A
L503, L505: 2.2u; L_Vishay_IHLP-2020; Tolerance Ip>2.9A, Irms>2.1A
L504: 1.5u; L_Sumida_CR75; Tolerance Ip>2.8A, Irms>2.1A
L506: 3.3u; L_TDK_7065; Tolerance Ipeek>3.7A, Irms>2.3A
Q501: Q_PMOS_DGS; TO-220-3_Vertical
R507: 5.6M; R_0805_2012Metric_Pad1.20x1.40mm_HandSolder; Tolerance 1%
R508: 6.81k; R_0805_2012Metric_Pad1.20x1.40mm_HandSolder
R509, R511, R513: 22.1k; R_0805_2012Metric_Pad1.20x1.40mm_HandSolder
R510: 33k; R_0805_2012Metric_Pad1.20x1.40mm_HandSolder; Tolerance 1%
R512, R519: 73.2k; R_0805_2012Metric_Pad1.20x1.40mm_HandSolder
R514, R515, R516: 10k; R_0805_2012Metric_Pad1.20x1.40mm_HandSolder
R517: 30.1k; R_0805_2012Metric_Pad1.20x1.40mm_HandSolder; Tolerance 1%
R518, R520, R522: 22.1k; R_0805_2012Metric_Pad1.20x1.40mm_HandSolder; Tolerance 1%
R521: 124k; R_0805_2012Metric_Pad1.20x1.40mm_HandSolder; Tolerance 1%
TP501, TP502: TestPoint; TestPoint_Keystone_5015_Micro-Minature
U503, U504, U505: TPS54294; HTSSOP-16-1EP_4.4x5mm_P0.65mm_EP3x3mm

Connections:
1V0: C501.1, C504.1, L501.1, R508.1
1V8: C529.1, C532.1, L504.2, R517.1
1V9: C502.1, C505.1, L502.1, R507.1, R510.1
3V3: C530.1, C533.1, L505.2, R519.1
3V3ADC: C503.1, C506.1, L503.1, R512.1
5V0: C531.1, C534.1, L506.2, R521.1
GND: C501.2, C502.2, C503.2, C504.2, C505.2, C506.2, C507.2, C508.2, C509.2, C510.2, C511.2, C512.2, C513.2, C517.1, C518.1, C519.1, C523.2, C524.2, C525.2, C526.2, C527.2, C528.2, C529.2, C530.2, C531.2, C532.2, C533.2, C534.2, J510.2, J511.2, J512.2, Q501.1 (G), R509.2, R511.2, R513.2, R518.1, R520.2, R522.2, U503.4 (PGND1), U503.8 (GND), U503.13 (PGND2), U503.17 (PwPd), U504.4 (PGND1), U504.8 (GND), U504.13 (PGND2), U504.17 (PwPd), U505.4 (PGND1), U505.8 (GND), U505.13 (PGND2), U505.17 (PwPd)
unnamed: C514.1, U503.2 (VBST1)
unnamed: C514.2, L501.2, U503.3 (SW1)
unnamed: C515.1, U504.2 (VBST1)
unnamed: C515.2, L502.2, U504.3 (SW1)
unnamed: C516.1, U505.2 (VBST1)
unnamed: C516.2, L503.2, U505.3 (SW1)
unnamed: C517.2, R514.1, R515.1, U503.9 (VREG5)
unnamed: C518.2, R516.1, U504.9 (VREG5)
unnamed: C519.2, U505.9 (VREG5)
unnamed: C520.1, U503.15 (VBST2)
unnamed: C520.2, L504.1, U503.14 (SW2)
unnamed: C521.1, U504.15 (VBST2)
unnamed: C521.2, L505.1, U504.14 (SW2)
unnamed: C522.1, U505.15 (VBST2)
unnamed: C522.2, L506.1, U505.14 (SW2)
unnamed: J509.5 (GND), J509.6 (Shield), J510.3
unnamed: J510.1, J511.1, J512.1, Q501.2 (D)
unnamed: R507.2, R510.2, R511.1, U504.7 (VFB1)
unnamed: R508.2, R509.1, U503.7 (VFB1)
unnamed: R512.2, R513.1, U505.7 (VFB1)
unnamed: R514.2, U503.6 (PG1), U503.12 (EN2)
unnamed: R515.2, TP502.1, U503.11 (PG2), U504.12 (EN2)
unnamed: R516.2, TP501.1, U504.5 (EN1), U504.11 (PG2), U505.5 (EN1), U505.12 (EN2)
unnamed: R517.2, R518.2, U503.10 (VFB2)
unnamed: R519.2, R520.1, U504.10 (VFB2)
unnamed: R521.2, R522.1, U505.10 (VFB2)
VIN: C507.1, C508.1, C509.1, C510.1, C511.1, C512.1, C513.1, C523.1, C524.1, C525.1, C526.1, C527.1, C528.1, J509.1 (VBUS), Q501.3 (S), U503.1 (VIN1), U503.5 (EN1), U503.16 (VIN2), U504.1 (VIN1), U504.16 (VIN2), U505.1 (VIN1), U505.16 (VIN2)

Notes on the sheet:
Power on order: 1.0V -> 1.8V -> 3.3V -> 1.9V 3.3VADC 5.0V
All outputs are rated for max 2A. The power input is probably a worse bottleneck.
Connect sensitive SSx and VFBx returens to GND at a single point
4.5V-18V
Reverse polarity protection
USB disconnects when barrel jack attached
Positive core
